bpcmusic/telex/extras/ii.png

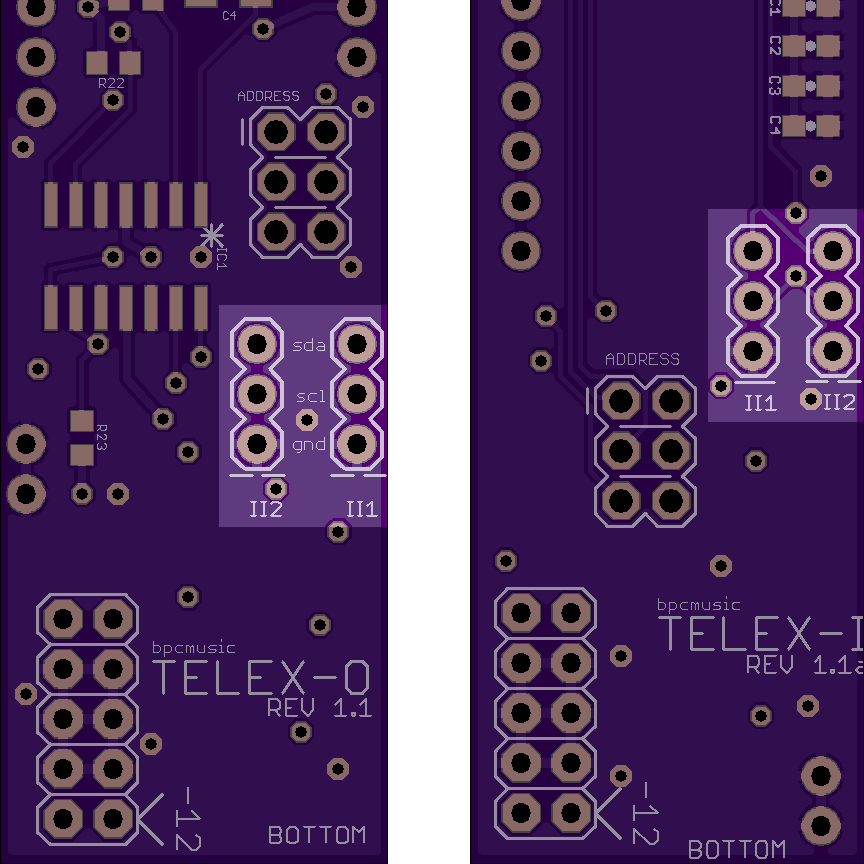
extras/ii.png
