bpcmusic/telex/extras/telex_address.png

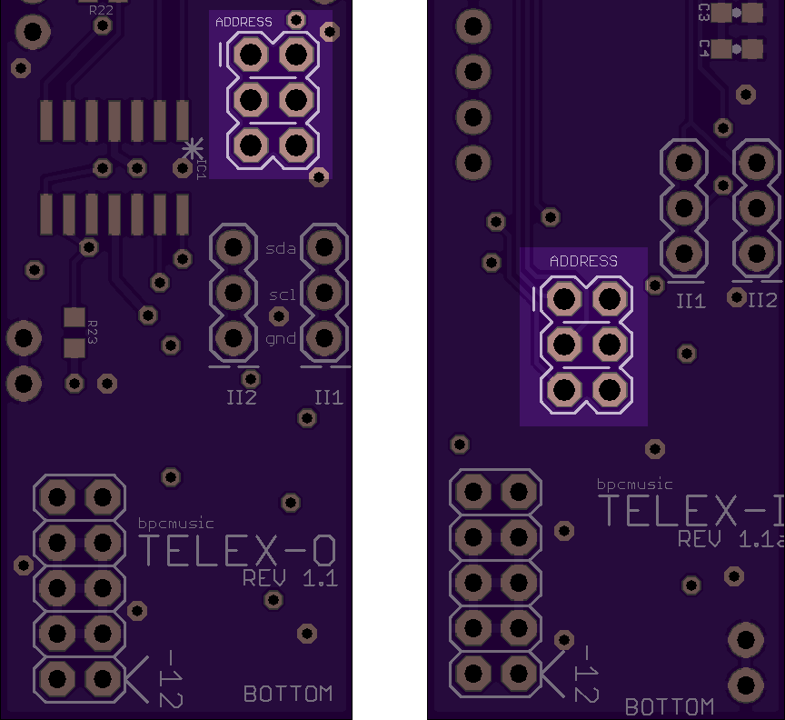
extras/telex_address.png
