bpcmusic/telex/hardware/TELEXi/board/images/TXi_Top_Top.png

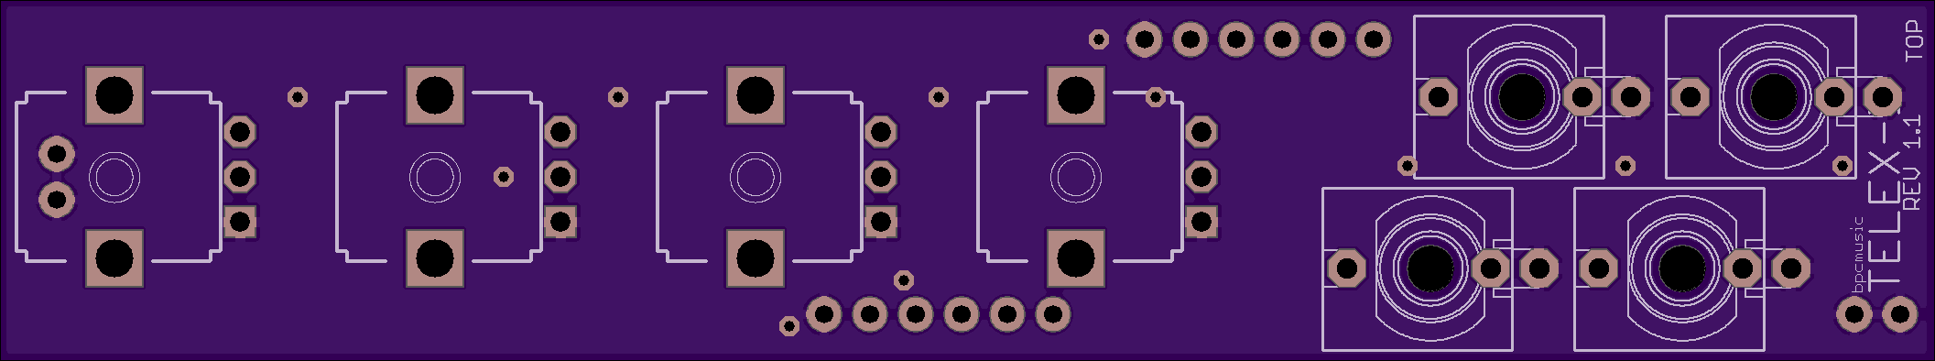
hardware/TELEXi/board/images/TXi_Top_Top.png
