bpcmusic/telex/hardware/TELEXi/board/stencil_frame/txi.png

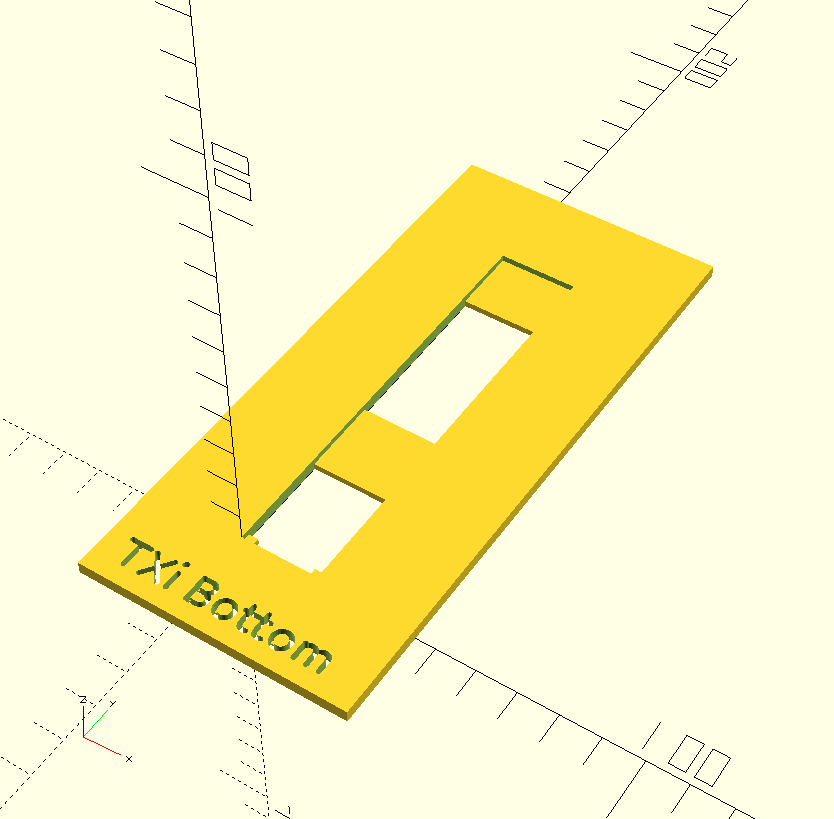
hardware/TELEXi/board/stencil_frame/txi.png
