bpcmusic/telex/hardware/TELEXo/board/images/TXo_Bottom_Top.png

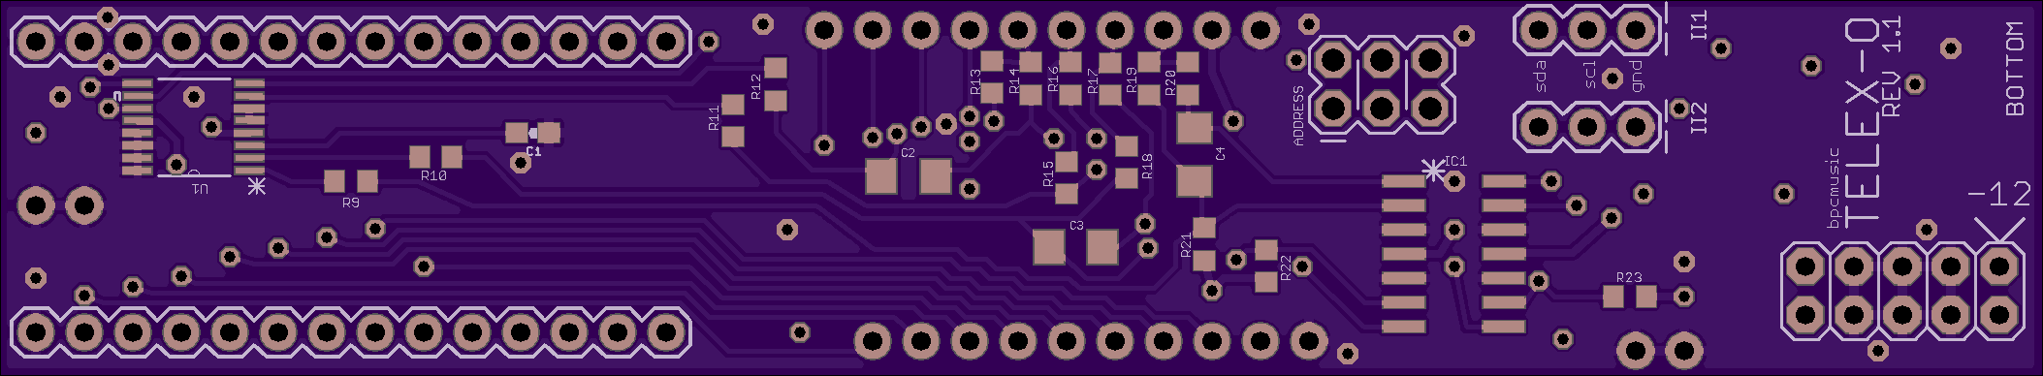
hardware/TELEXo/board/images/TXo_Bottom_Top.png
