bpcmusic/telex/hardware/TELEXo/board/stencil_frame/txo_bottom.png

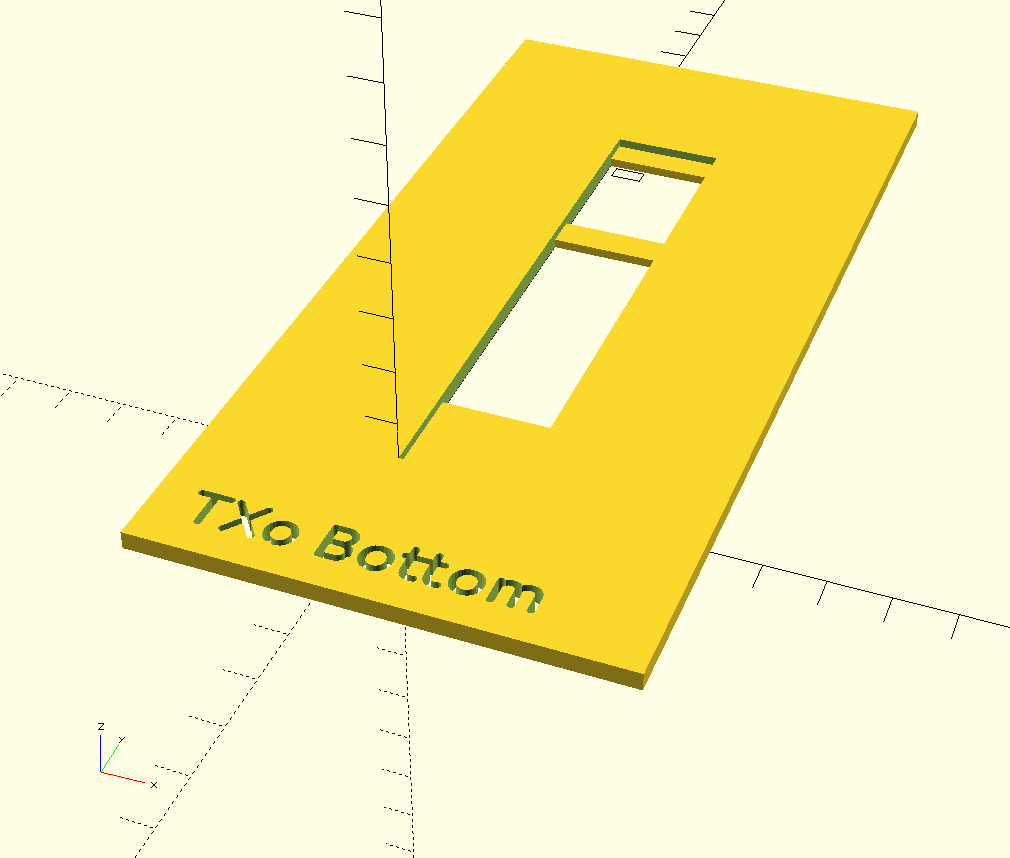
hardware/TELEXo/board/stencil_frame/txo_bottom.png
