bpcmusic/telex/hardware/TELEXo/board/stencil_frame/txo_top.png

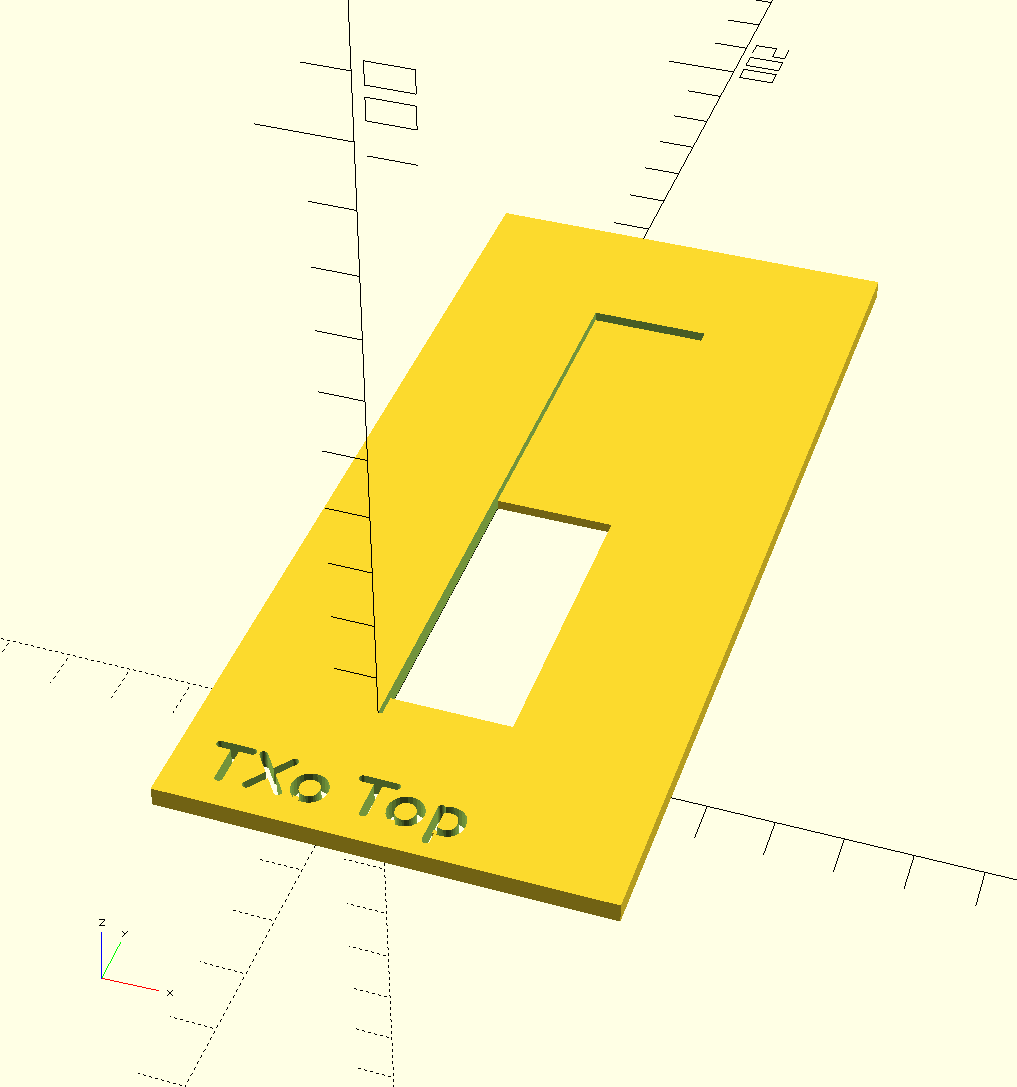
hardware/TELEXo/board/stencil_frame/txo_top.png
