bpcmusic/telex/telex.jpg

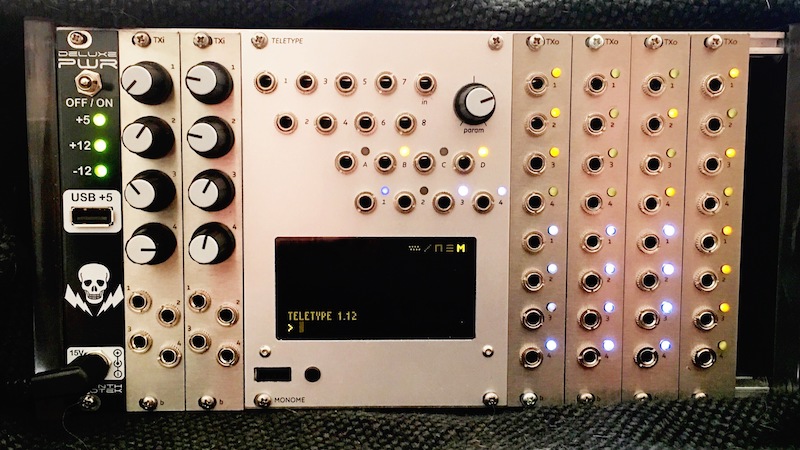
telex.jpg
