bpcmusic/telex/TX-MockUp.png

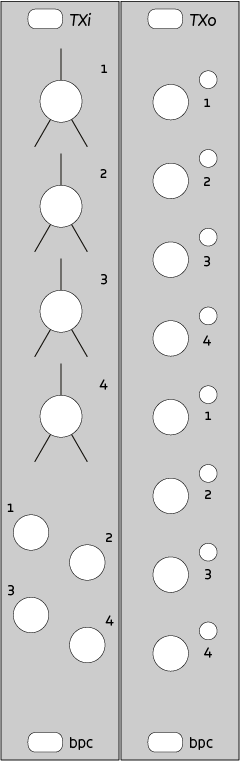
TX-MockUp.png
