bpcmusic/telex/hardware/TELEXi/board/build_map/tb/txi_tb_build_map.pdf

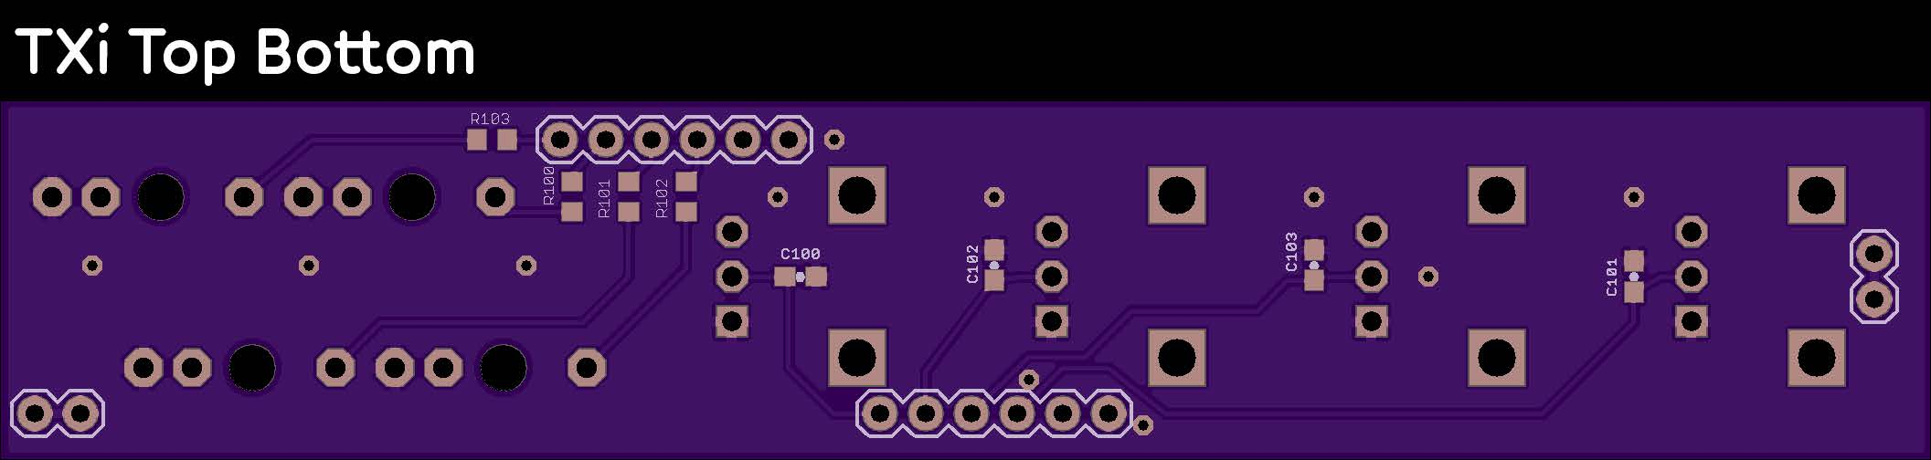
[picture p36: page 1]
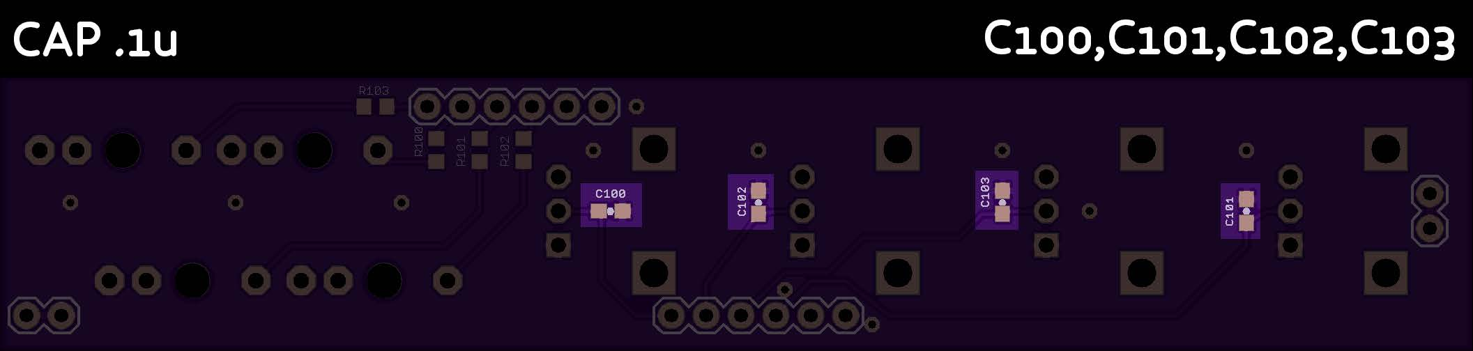
[picture p37: page 2]
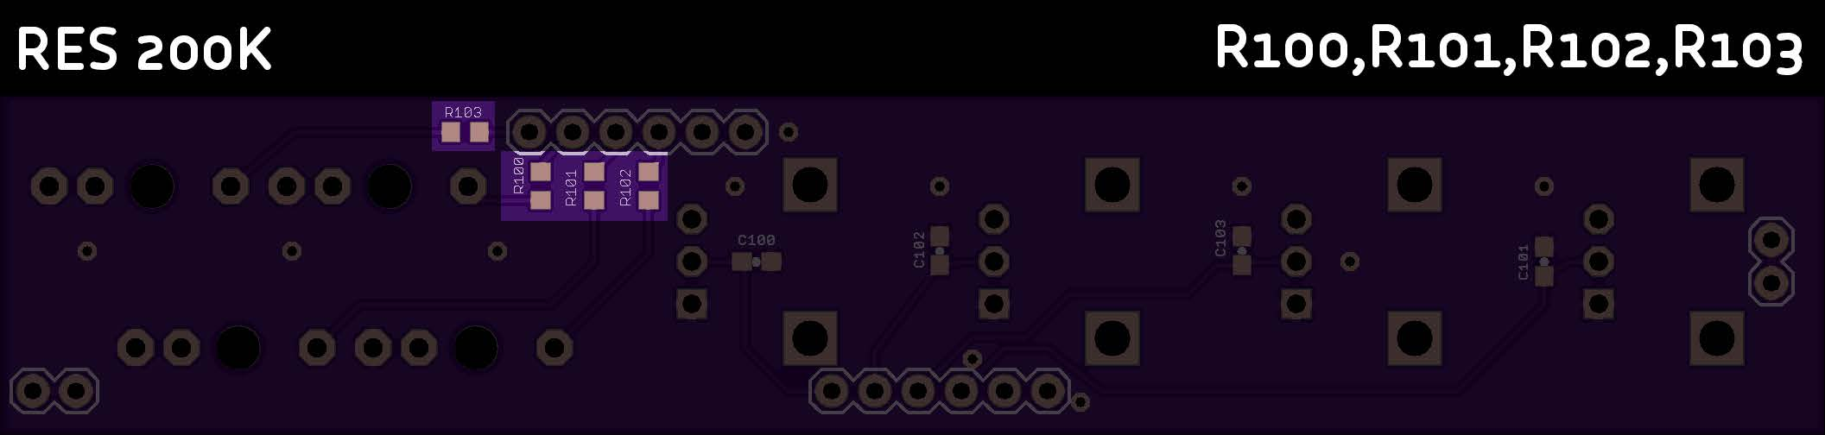
[picture p38: page 3]
