bpcmusic/telex/hardware/TELEXi/board/build_map/bb/00.png

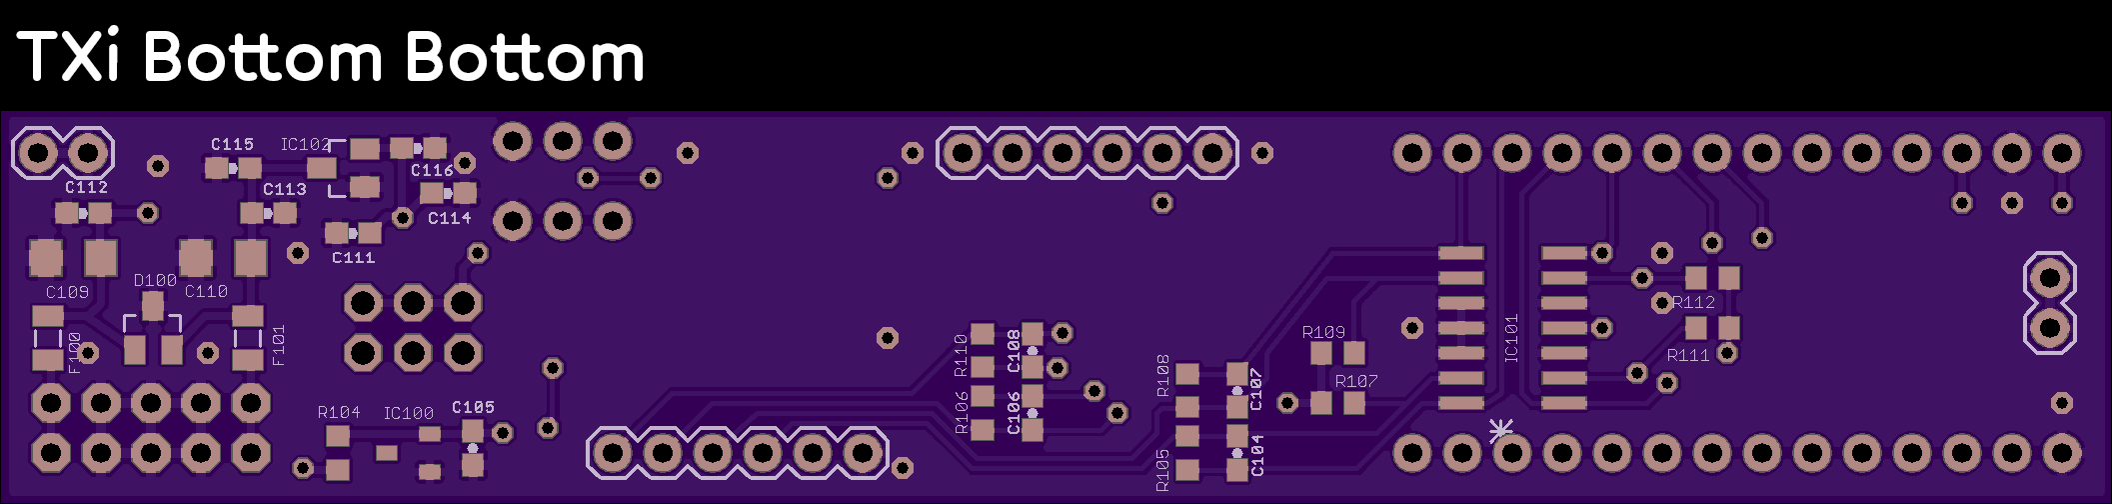
hardware/TELEXi/board/build_map/bb/00.png
