bpcmusic/telex/hardware/TELEXi/board/build_map/bb/01.png

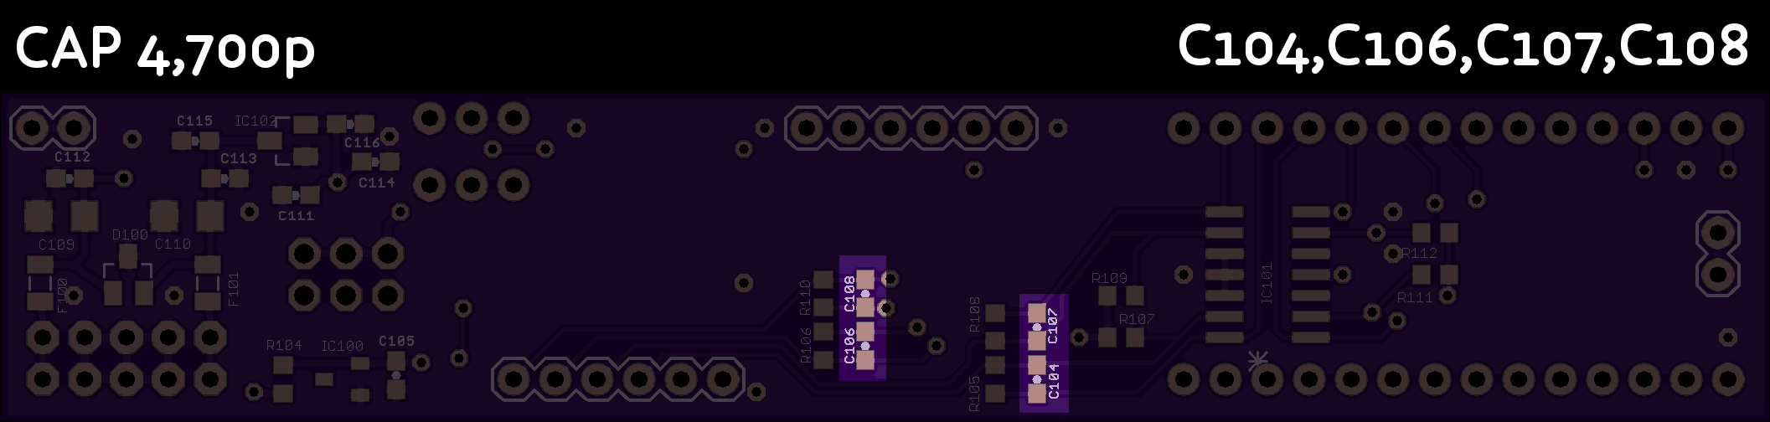
hardware/TELEXi/board/build_map/bb/01.png
