bpcmusic/telex/hardware/TELEXi/board/build_map/bb/02.png

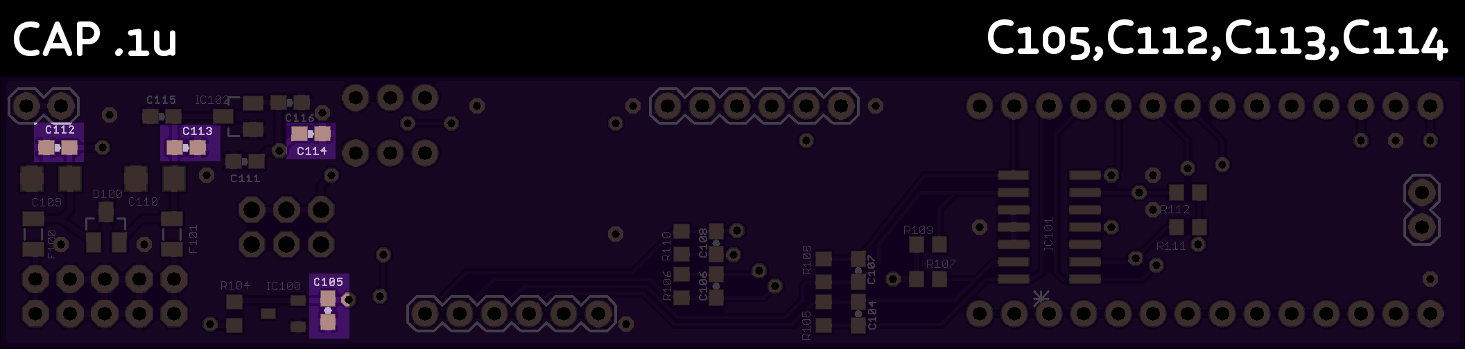
hardware/TELEXi/board/build_map/bb/02.png
