bpcmusic/telex/hardware/TELEXi/board/build_map/bb/03.png

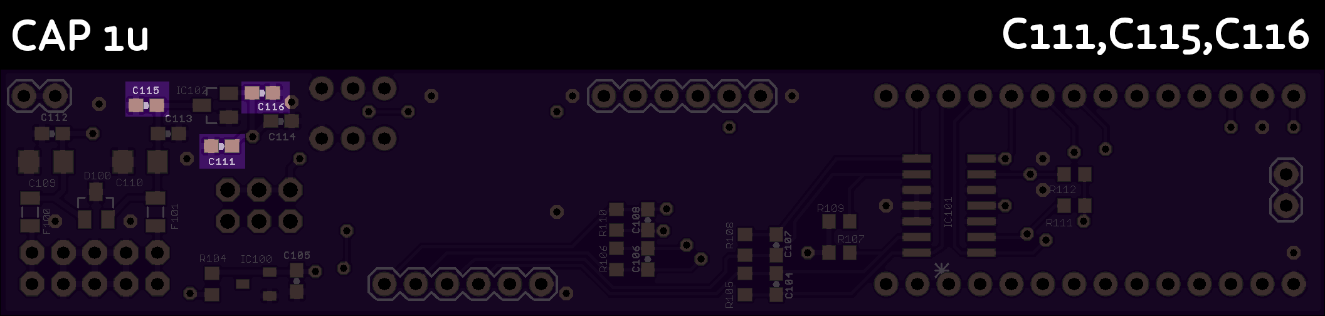
hardware/TELEXi/board/build_map/bb/03.png
