bpcmusic/telex/hardware/TELEXi/board/build_map/bb/04.png

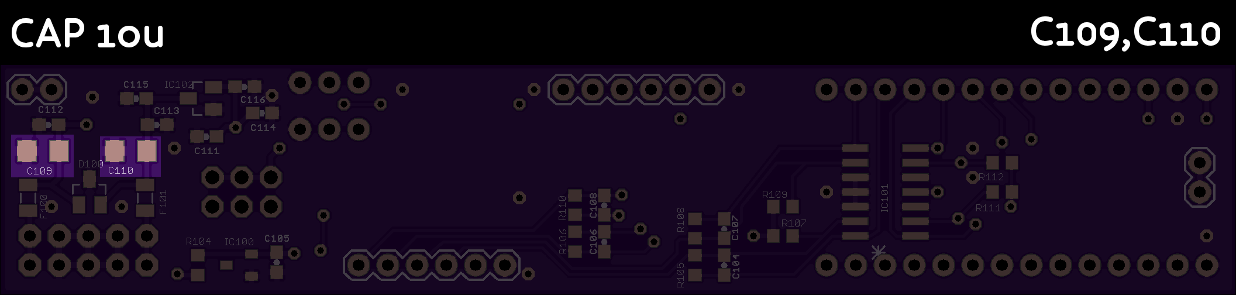
hardware/TELEXi/board/build_map/bb/04.png
