bpcmusic/telex/hardware/TELEXi/board/build_map/bb/06.png

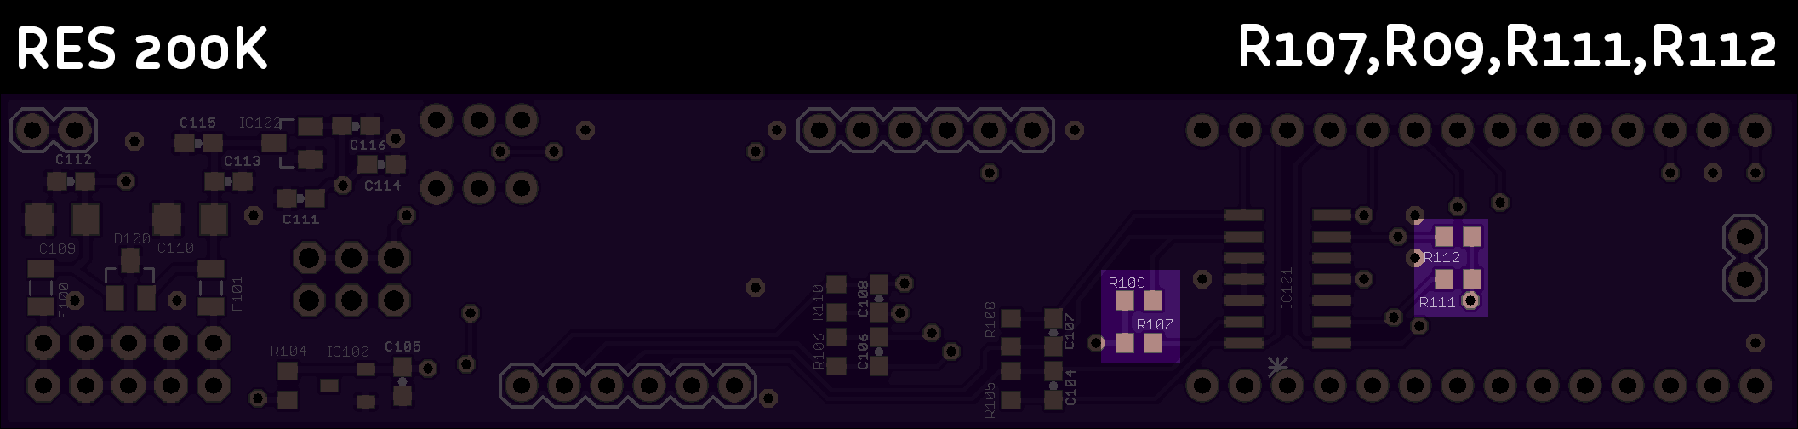
hardware/TELEXi/board/build_map/bb/06.png
