bpcmusic/telex/hardware/TELEXi/board/build_map/bb/08.png

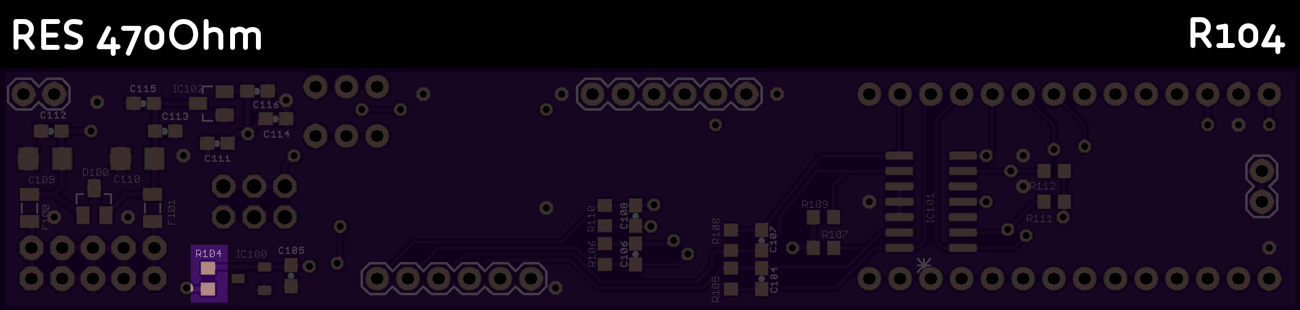
hardware/TELEXi/board/build_map/bb/08.png
