bpcmusic/telex/hardware/TELEXi/board/build_map/bb/09.png

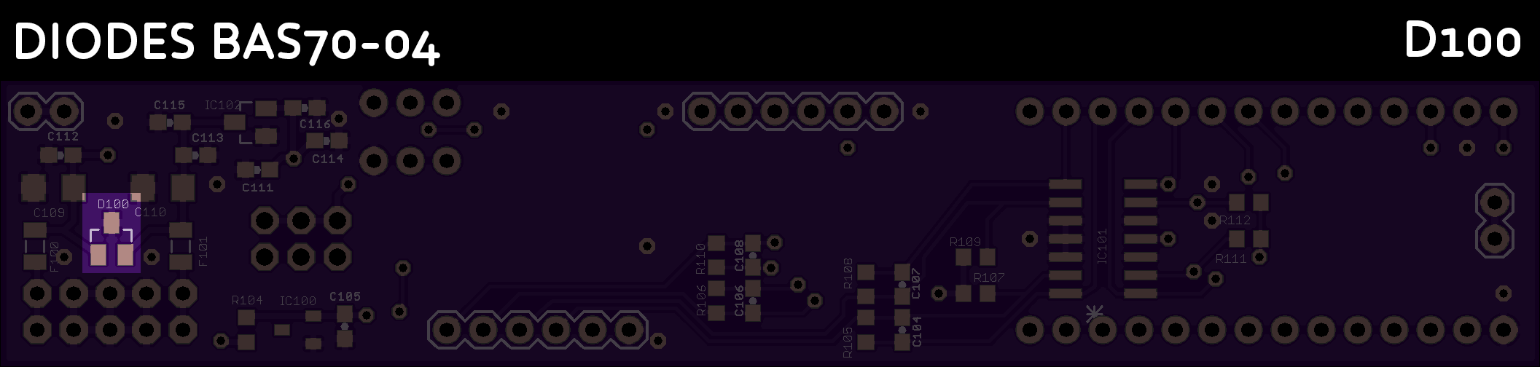
hardware/TELEXi/board/build_map/bb/09.png
