bpcmusic/telex/hardware/TELEXi/board/build_map/bb/10.png

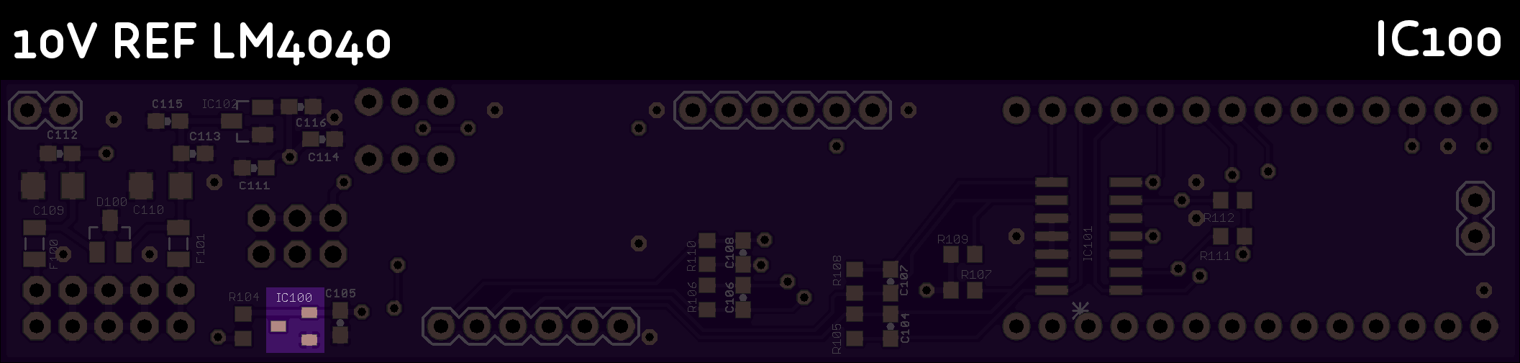
hardware/TELEXi/board/build_map/bb/10.png
