bpcmusic/telex/hardware/TELEXi/board/build_map/bb/11.png

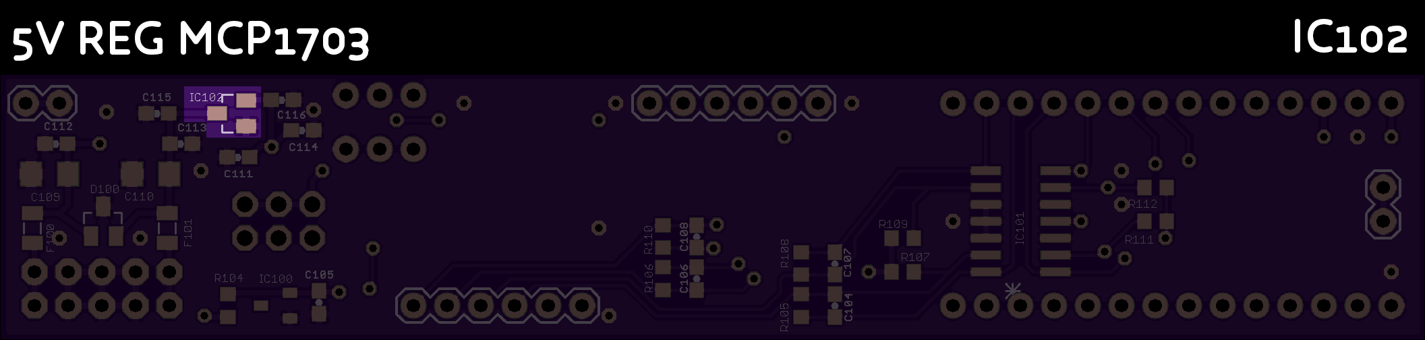
hardware/TELEXi/board/build_map/bb/11.png
