bpcmusic/telex/hardware/TELEXi/board/build_map/bb/12.png

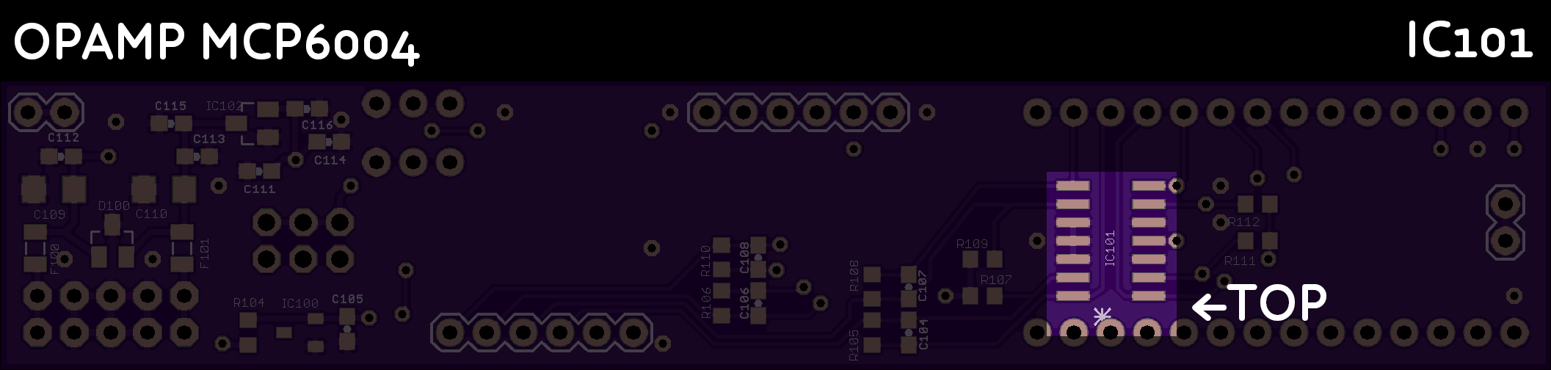
hardware/TELEXi/board/build_map/bb/12.png
