bpcmusic/telex/hardware/TELEXi/board/build_map/bt/00.png

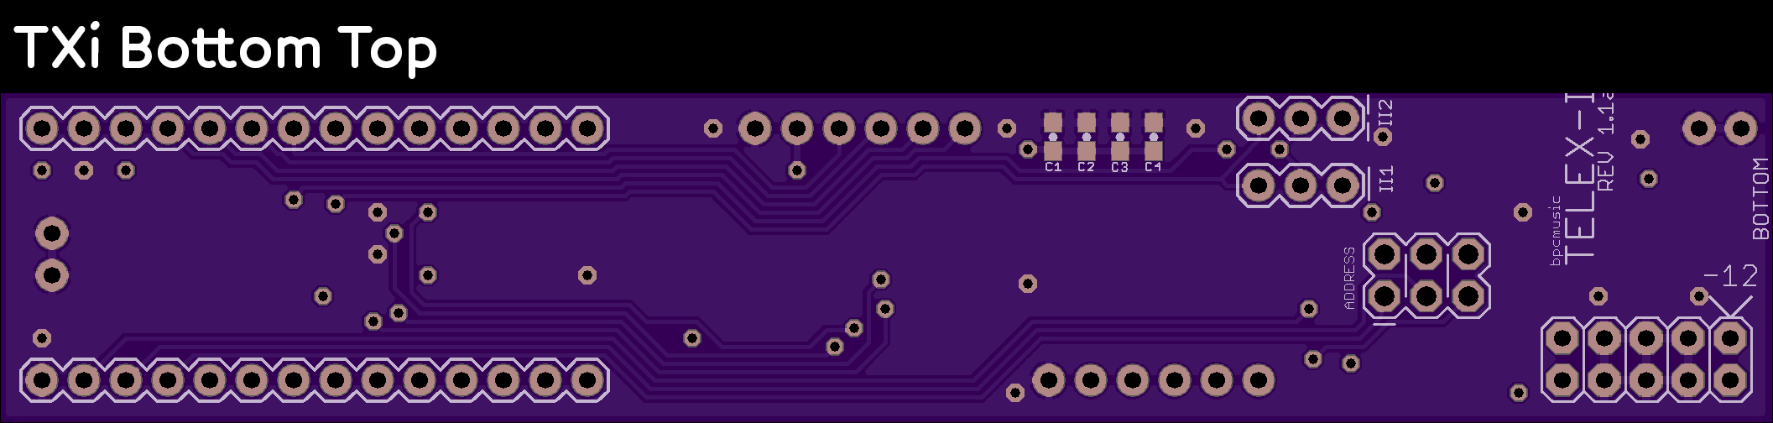
hardware/TELEXi/board/build_map/bt/00.png
