bpcmusic/telex/hardware/TELEXi/board/build_map/bt/01.png

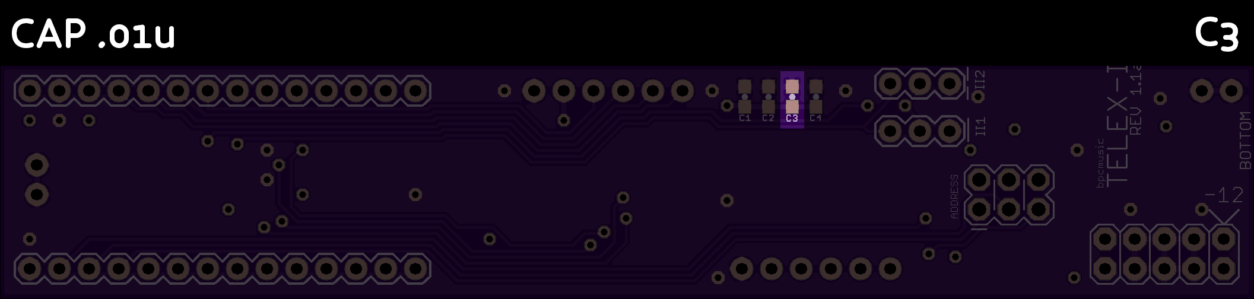
hardware/TELEXi/board/build_map/bt/01.png
