bpcmusic/telex/hardware/TELEXo/board/build_map/bb/00.png

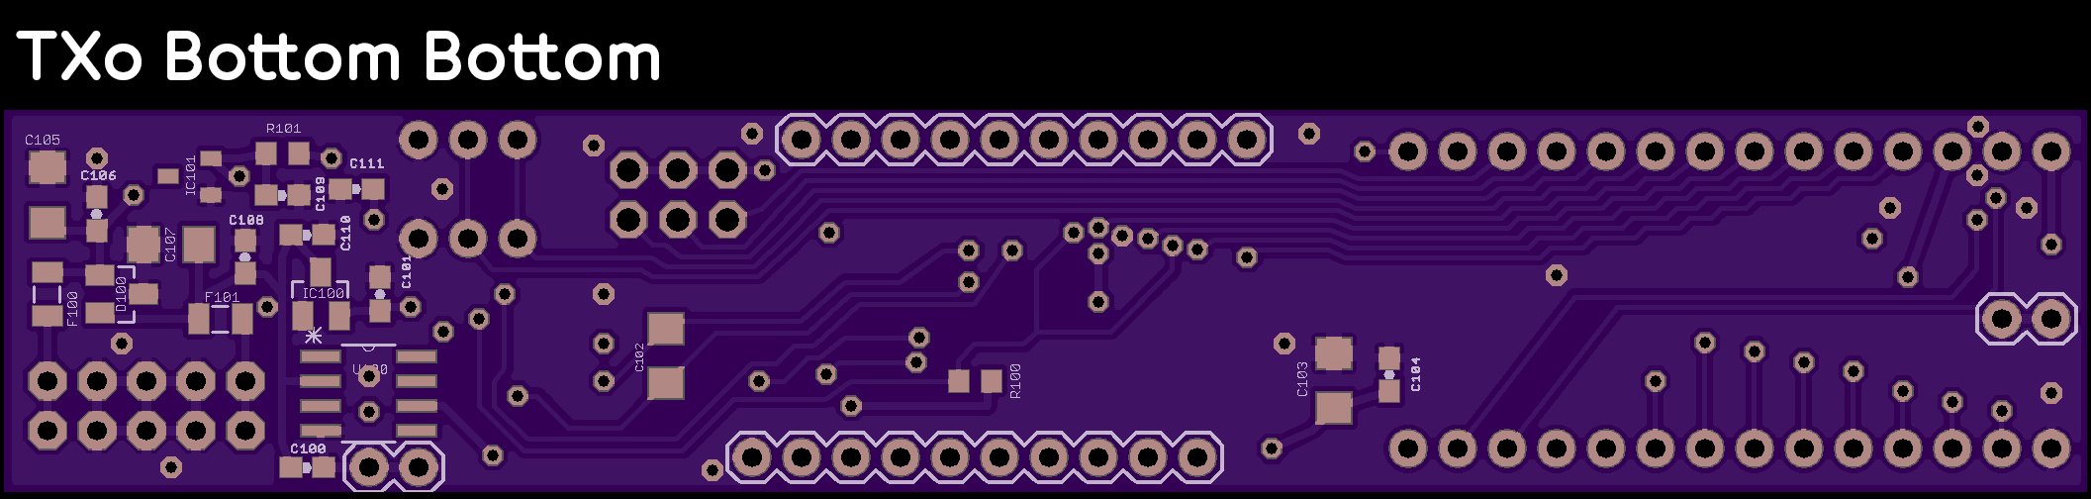
hardware/TELEXo/board/build_map/bb/00.png
