bpcmusic/telex/hardware/TELEXo/board/build_map/bb/01.png

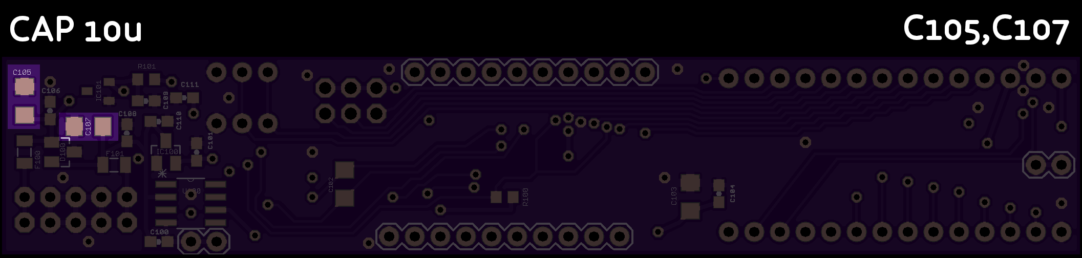
hardware/TELEXo/board/build_map/bb/01.png
