bpcmusic/telex/hardware/TELEXo/board/build_map/bb/02.png

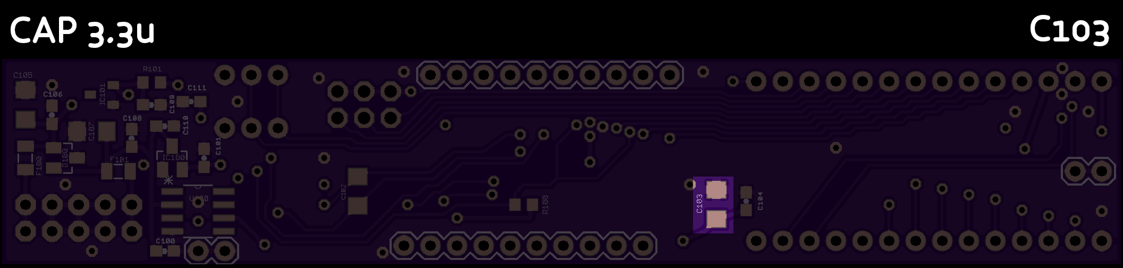
hardware/TELEXo/board/build_map/bb/02.png
