bpcmusic/telex/hardware/TELEXo/board/build_map/bb/03.png

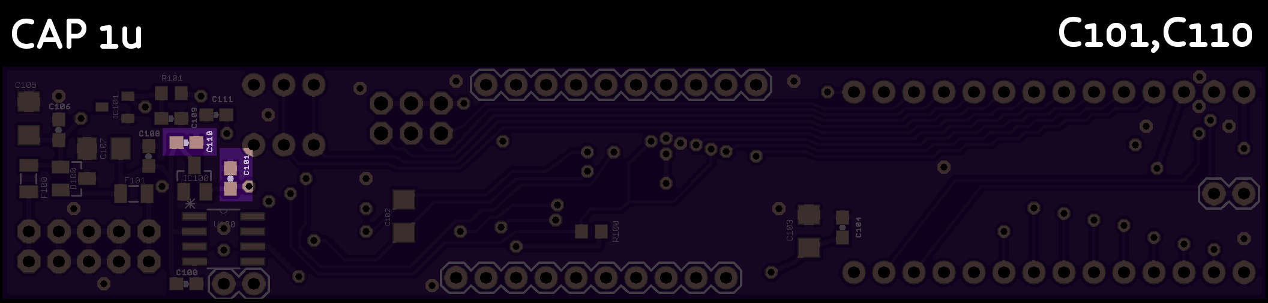
hardware/TELEXo/board/build_map/bb/03.png
