bpcmusic/telex/hardware/TELEXo/board/build_map/bb/04.png

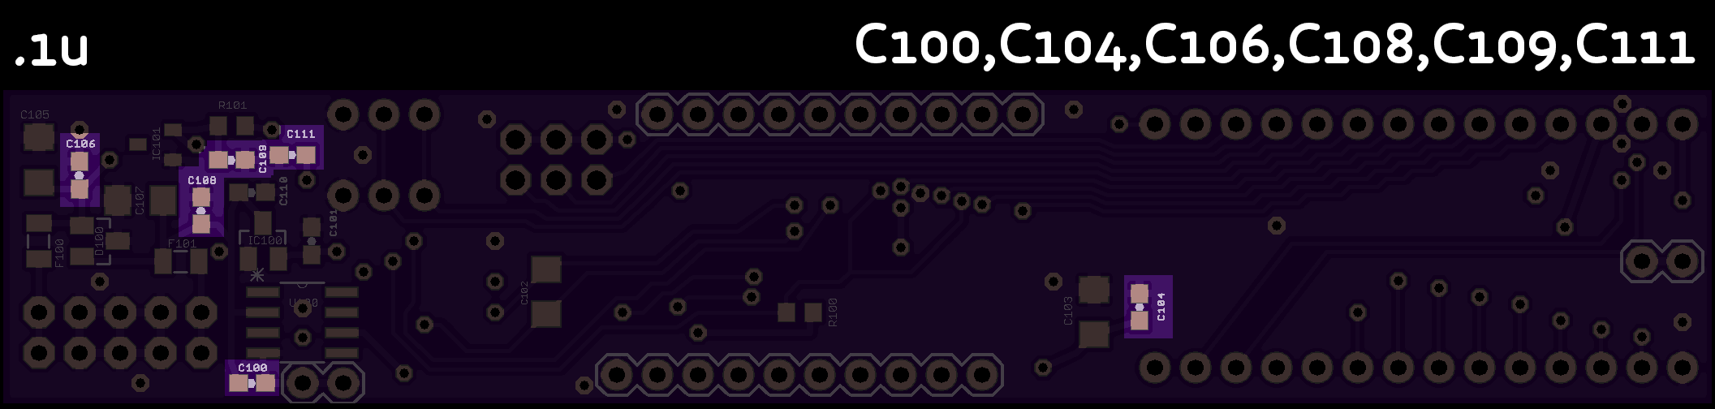
hardware/TELEXo/board/build_map/bb/04.png
