bpcmusic/telex/hardware/TELEXo/board/build_map/bb/05.png

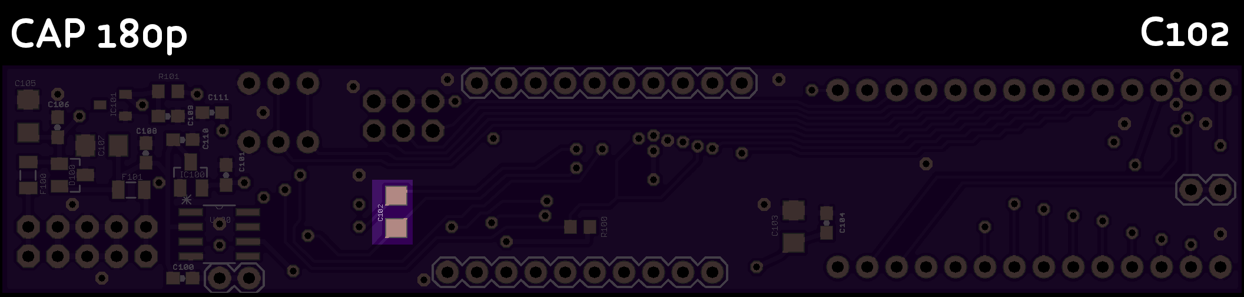
hardware/TELEXo/board/build_map/bb/05.png
