bpcmusic/telex/hardware/TELEXo/board/build_map/bb/09.png

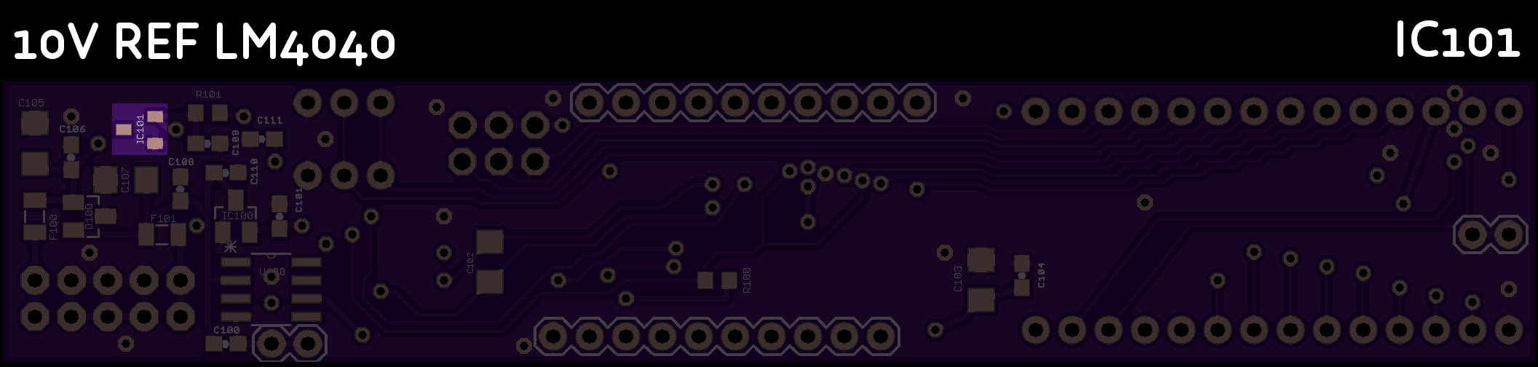
hardware/TELEXo/board/build_map/bb/09.png
