bpcmusic/telex/hardware/TELEXo/board/build_map/bb/10.png

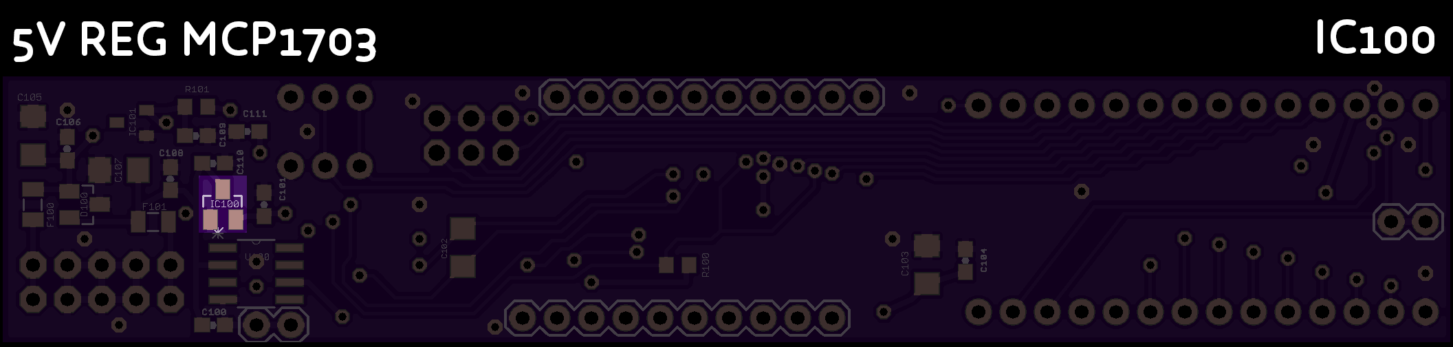
hardware/TELEXo/board/build_map/bb/10.png
