bpcmusic/telex/hardware/TELEXo/board/build_map/bb/11.png

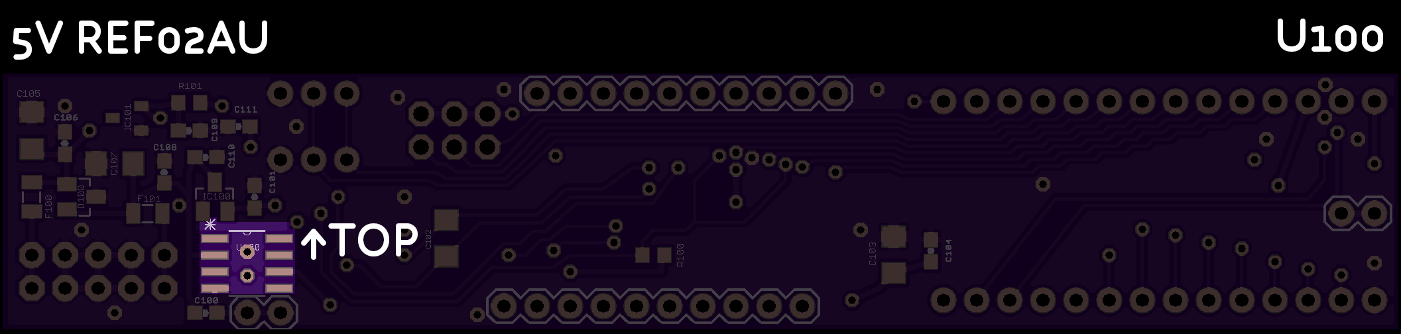
hardware/TELEXo/board/build_map/bb/11.png
