bpcmusic/telex/hardware/TELEXo/board/build_map/bb/12.png

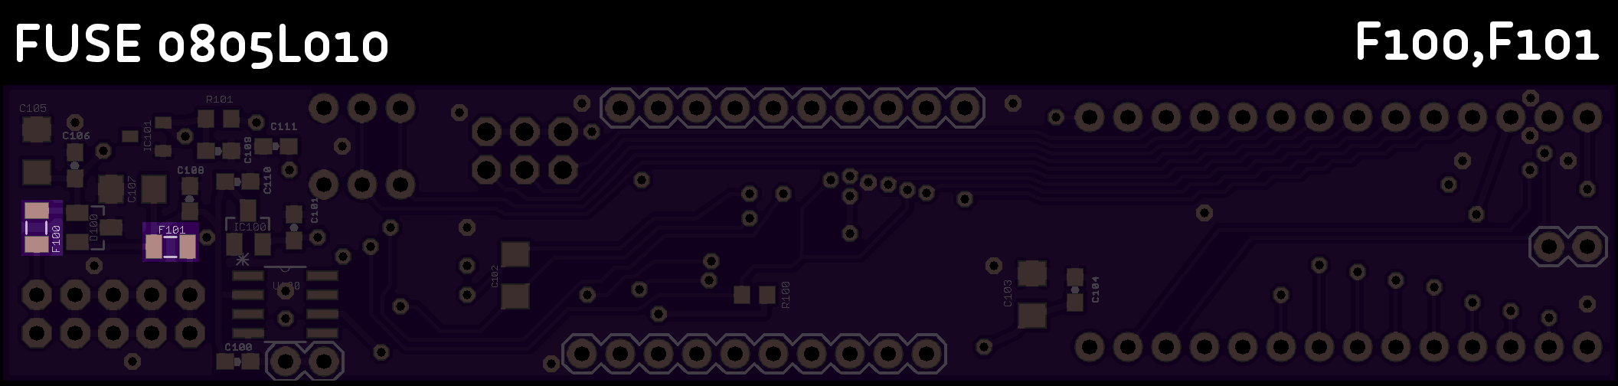
hardware/TELEXo/board/build_map/bb/12.png
