bpcmusic/telex/hardware/TELEXo/board/build_map/bt/00.png

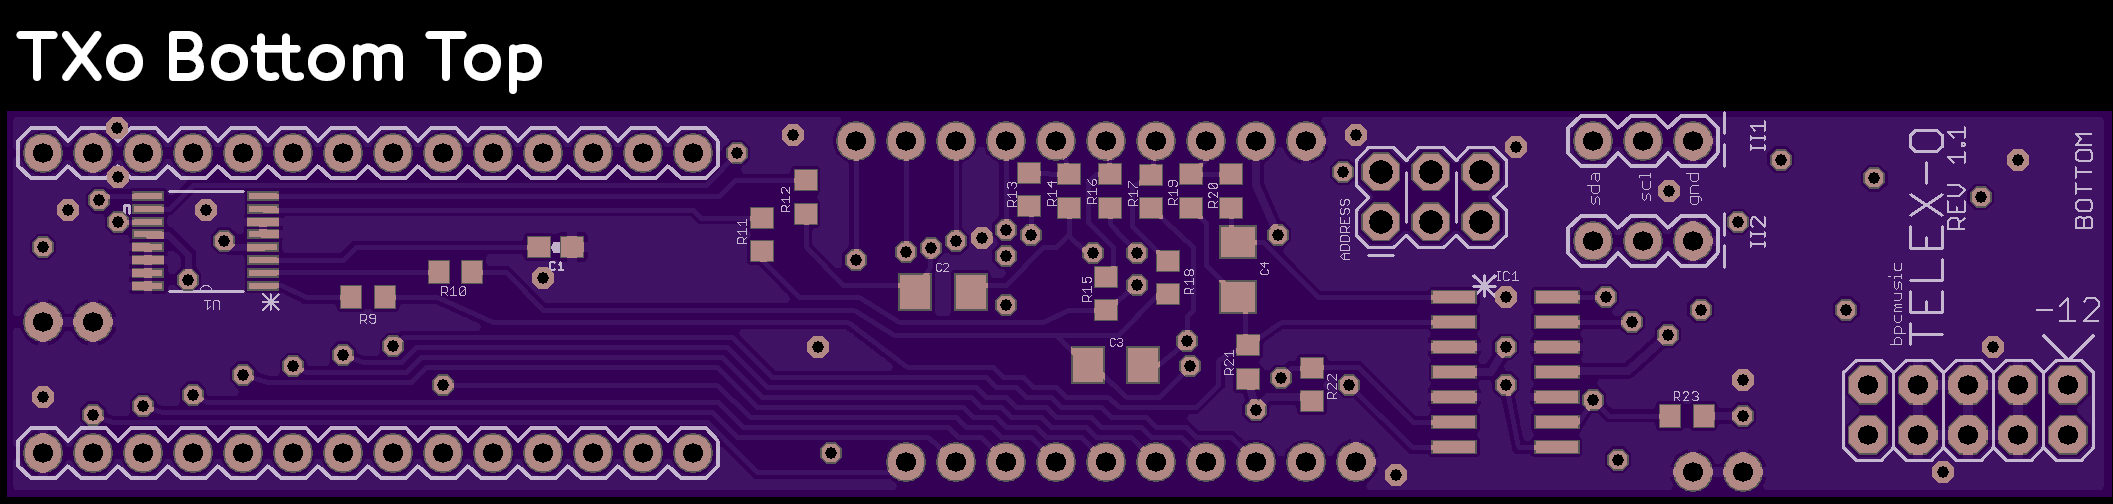
hardware/TELEXo/board/build_map/bt/00.png
