bpcmusic/telex/hardware/TELEXo/board/build_map/bt/01.png

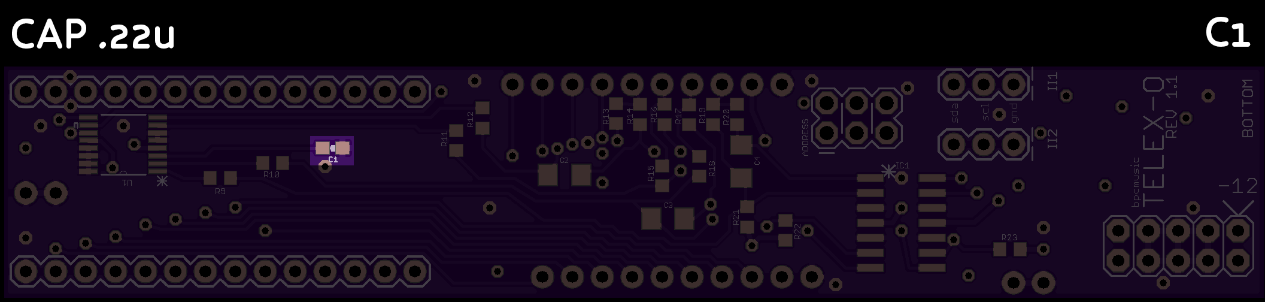
hardware/TELEXo/board/build_map/bt/01.png
