bpcmusic/telex/hardware/TELEXo/board/build_map/bt/02.png

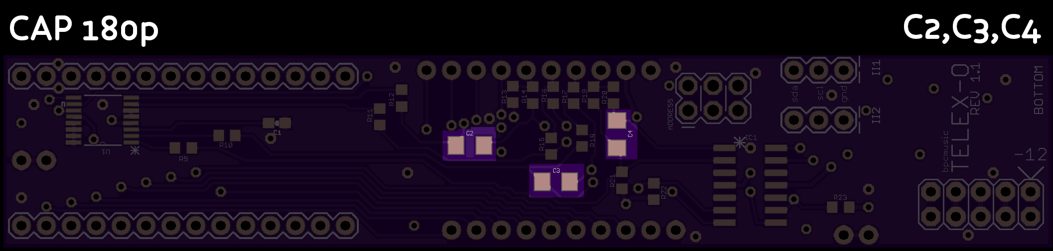
hardware/TELEXo/board/build_map/bt/02.png
