bpcmusic/telex/hardware/TELEXo/board/build_map/bt/03.png

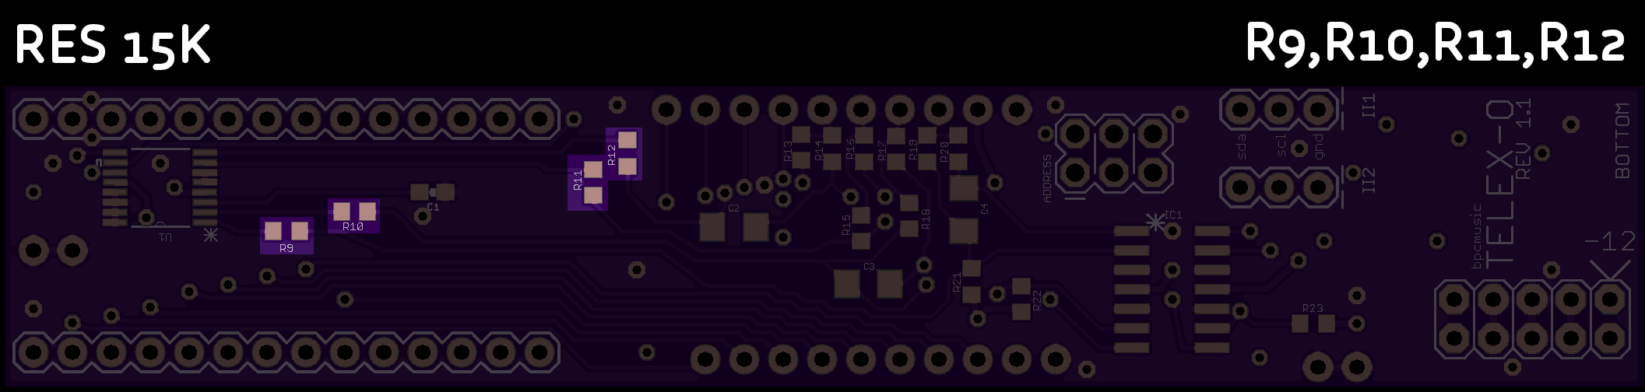
hardware/TELEXo/board/build_map/bt/03.png
