bpcmusic/telex/hardware/TELEXo/board/build_map/bt/04.png

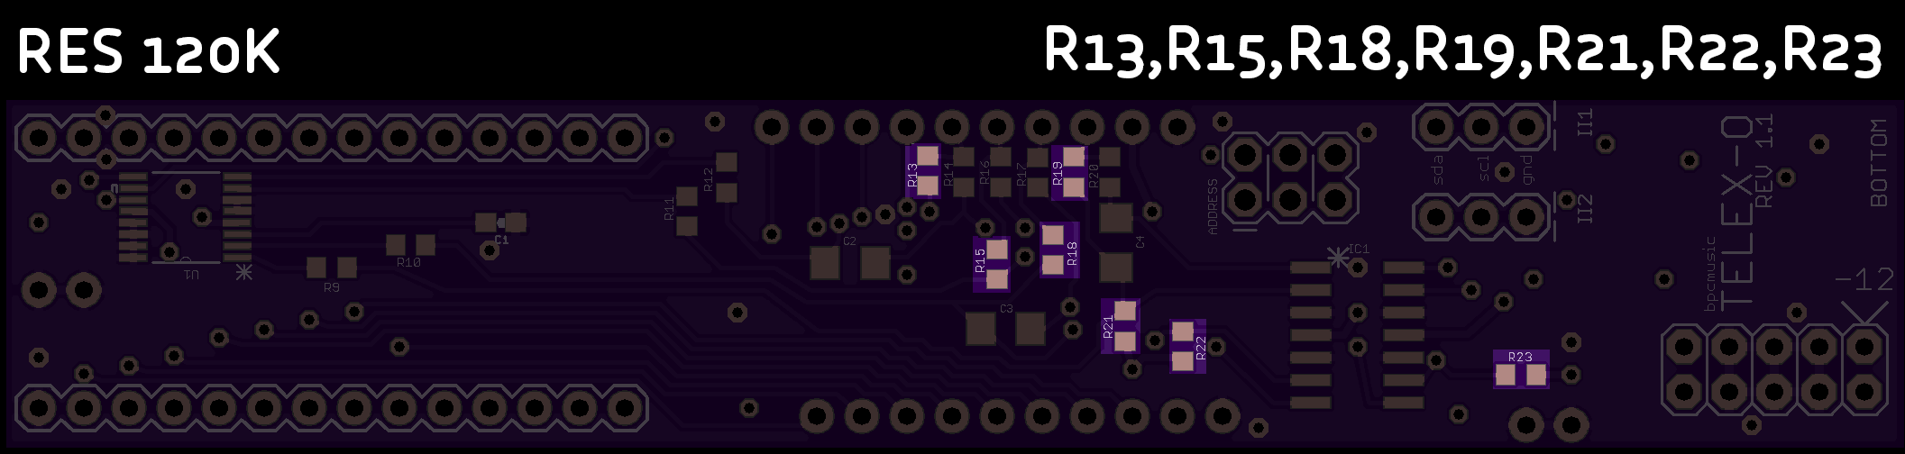
hardware/TELEXo/board/build_map/bt/04.png
