bpcmusic/telex/hardware/TELEXo/board/build_map/bt/05.png

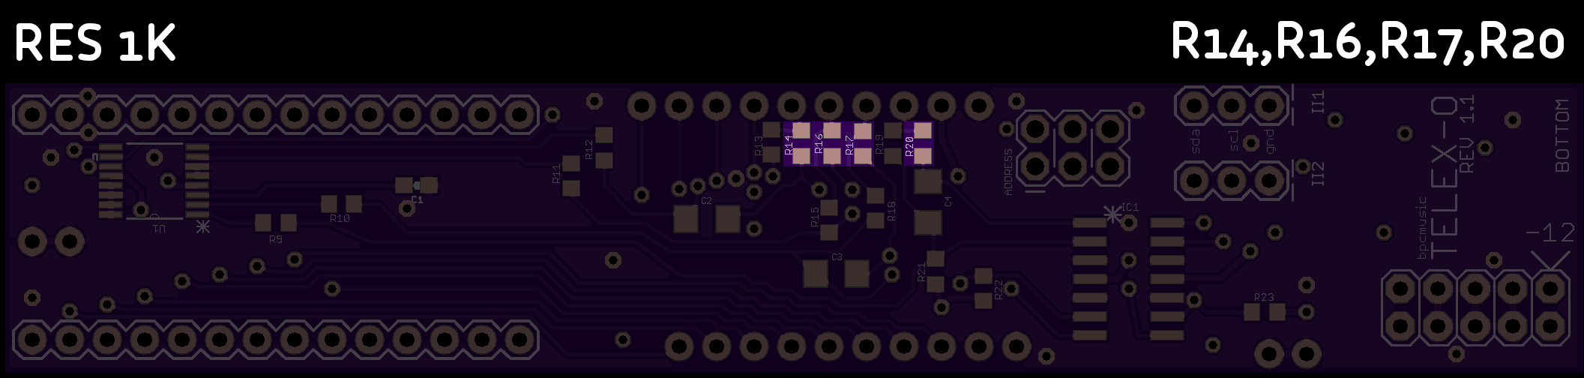
hardware/TELEXo/board/build_map/bt/05.png
