bpcmusic/telex/hardware/TELEXo/board/build_map/bt/06.png

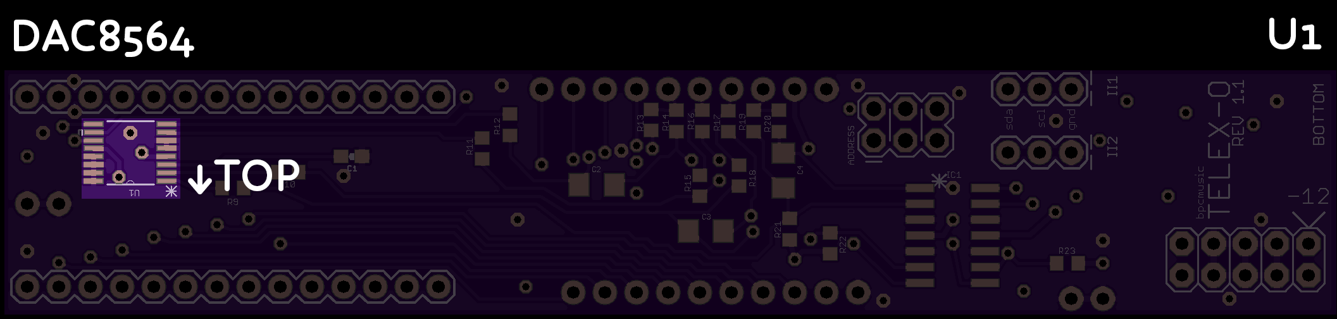
hardware/TELEXo/board/build_map/bt/06.png
