bpcmusic/telex/hardware/TELEXo/board/build_map/bt/07.png

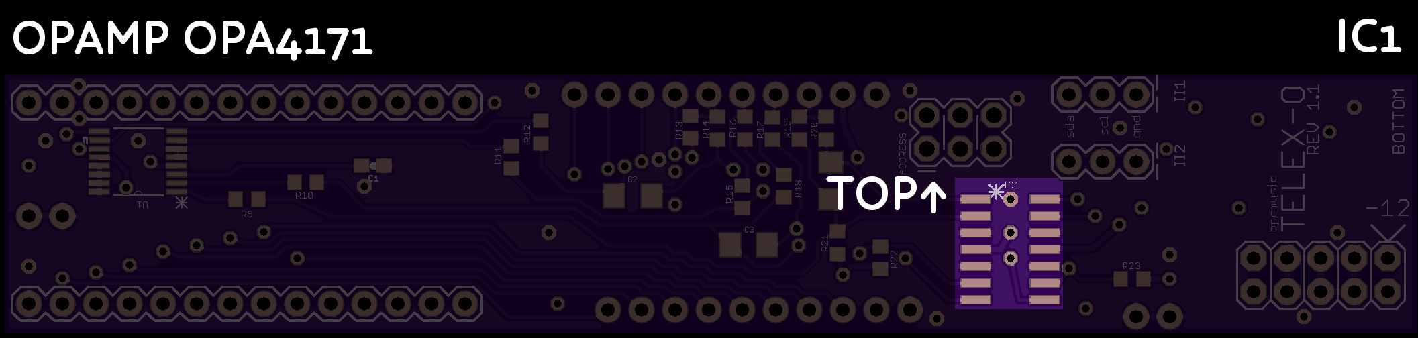
hardware/TELEXo/board/build_map/bt/07.png
