bpcmusic/telex/hardware/TELEXo/board/build_map/tb/00.png

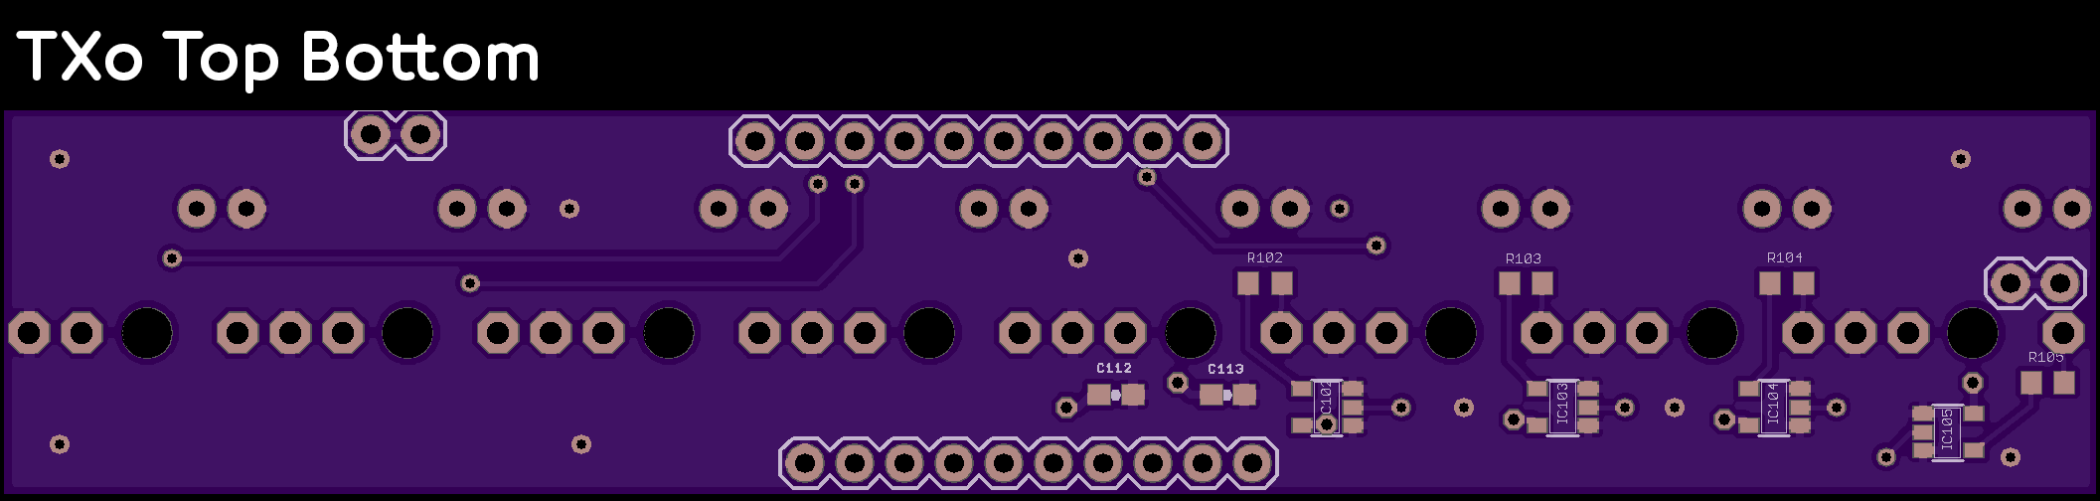
hardware/TELEXo/board/build_map/tb/00.png
