bpcmusic/telex/hardware/TELEXo/board/build_map/tb/01.png

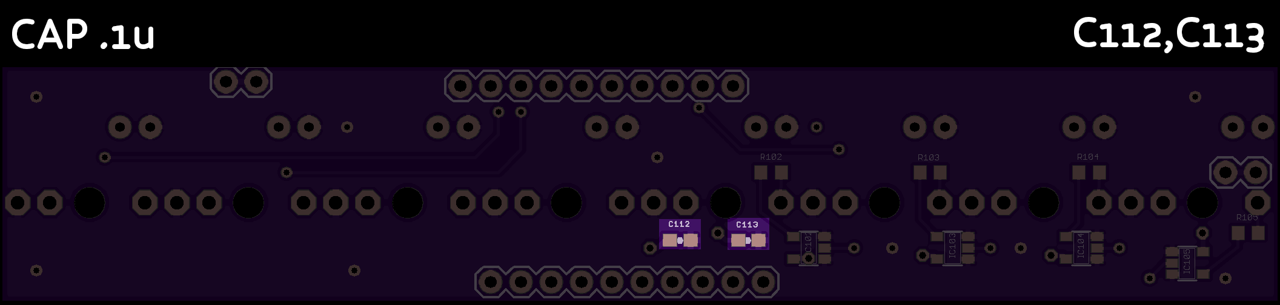
hardware/TELEXo/board/build_map/tb/01.png
