bpcmusic/telex/hardware/TELEXo/board/build_map/tb/02.png

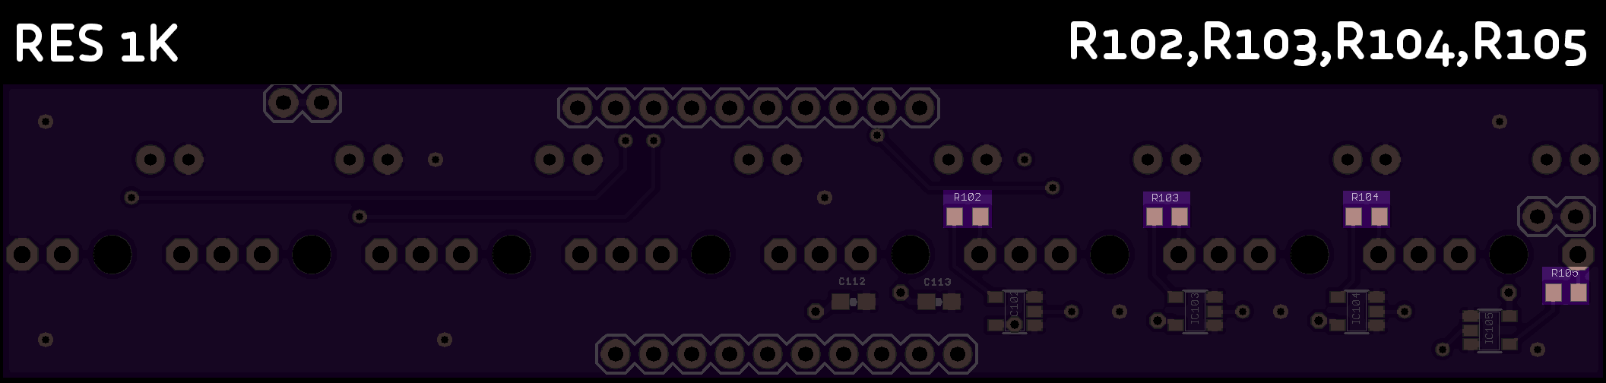
hardware/TELEXo/board/build_map/tb/02.png
