bpcmusic/telex/hardware/TELEXo/board/build_map/tb/03.png

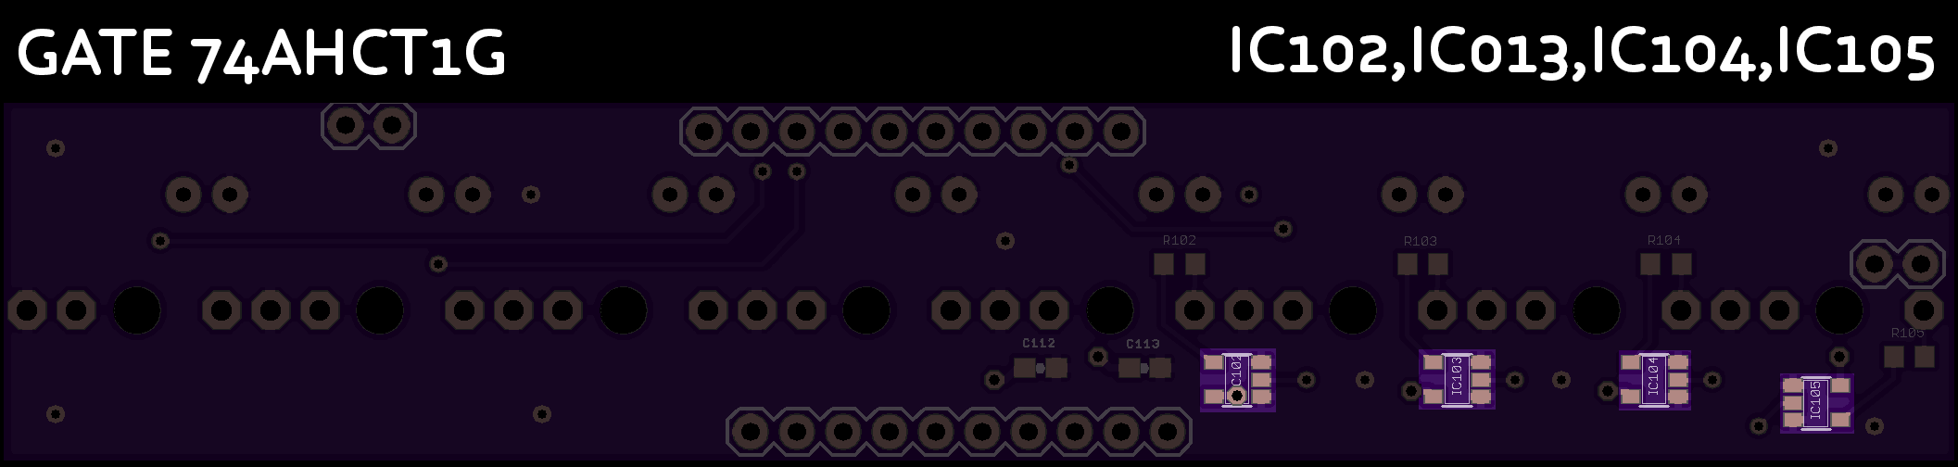
hardware/TELEXo/board/build_map/tb/03.png
