bpcmusic/telex/hardware/TELEXo/board/build_map/tt/00.png

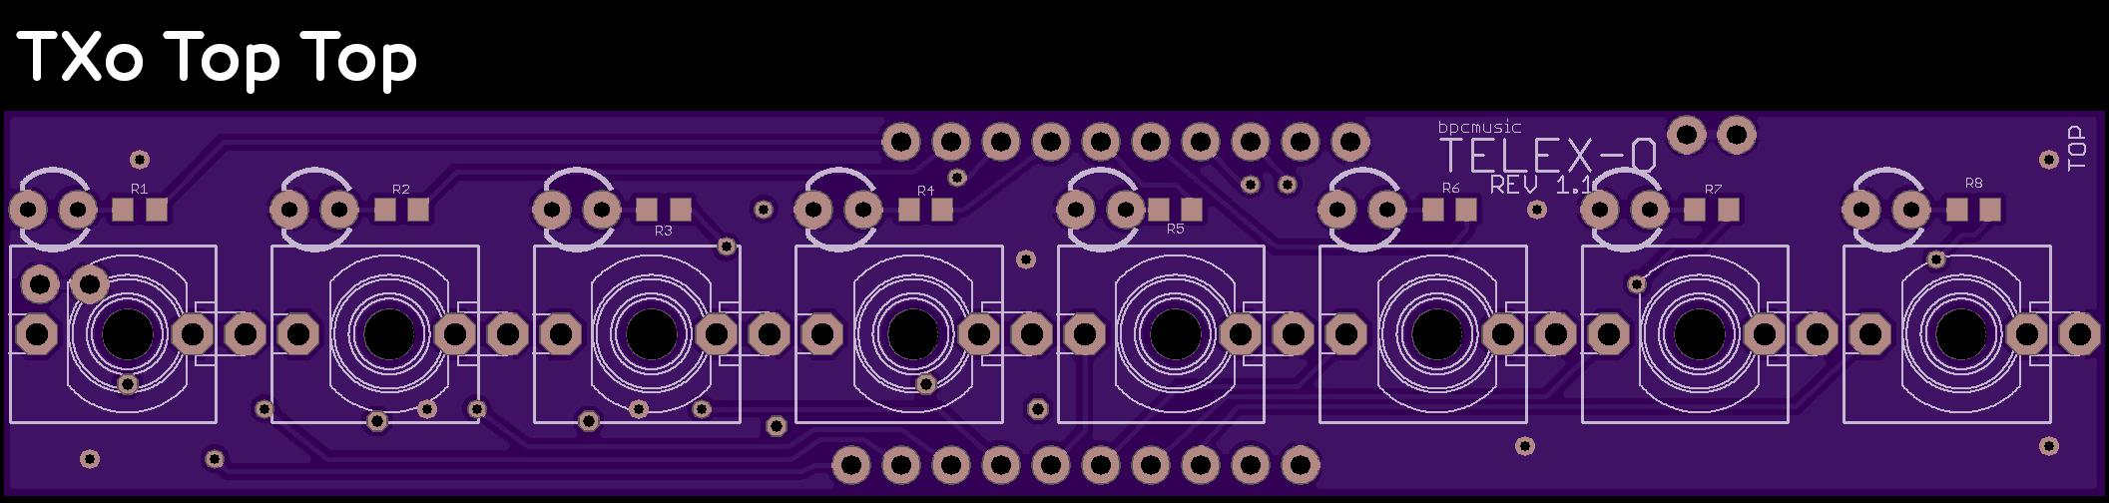
hardware/TELEXo/board/build_map/tt/00.png
