bpcmusic/telex/software/TELEXo/Quantizer.cpp

/*
 * TELEXo Eurorack Module
 * (c) 2016, 2017 Brendon Cassidy
 * MIT License
 */
 
#include "Arduino.h"
#include "Quantizer.h"
#include "TxHelper.h"

/*
 * initializes the quantizer and sets the scale to 0 (usually equal temperment)
 */
Quantizer::Quantizer() {
  Quantizer(0);
}

/*
 * initializes the quantizer and sets the initial scale
 */
Quantizer::Quantizer(int scale) {
  SetScale(scale);
  
  _last.Note = 0;
  _last.Value = 0;
  
  _below = 0;
  _above = 0;
  _noteMode = false;
}

/*
 * change the scale of the quantizer
 */
void Quantizer::SetScale(int scale) {
  if (scale < scaleCount)
    _scale = scale;
}

/*
 * quantizes an int (range 0-16383)
 */
QuantizeResponse Quantizer::Quantize(int in) {

  QuantizeResponse response;

  // deal with negative values
  in = in < 0 ? abs(in) : in;

  // short circuit if we are within our current bounary
  if (in >= _below && in < _above){
    return _last;
  }
  
  // if not - we need to find where we are in the list
  // hints are a type of skip-list that jumps us to the proper octave
  _octave = (int)(in / 1638.3) - 1;
  _octave = _octave > 0 ? _octave : 0;
  
  _index = hints[_scale][_octave];

  int distance = 32768;
  int distanceTemp = 0;

  // find where we can't get any closer then back out
  while (_index < notecount[_scale]) {

    _temp = in - scales[_scale][_index];
    
    distanceTemp = abs(_temp);

    if (distanceTemp > distance){
      _index--;
      break;
    } else {
      // else increment
      distance = distanceTemp;
      _index++;
    }
    
  }

  // move it down to the next to last if we made it to the end
  if (_index >= notecount[_scale]) 
    _index = notecount[_scale] - 1;
  
  // use index to quantize
  _current = scales[_scale][_index];

  // set the response
  response.Note = _index;
  response.Value = _current;
  response.Frequency = freqs[_scale][_index];
  
  _last = response;
  
  // now set the helper boundries
  _above = _index < notecount[_scale] - 1 ? scales[_scale][_index + 1] : 32767;
  _below = _index > 0 ? scales[_scale][_index-1] : scales[_scale][_index];

  // similar to a mutable quantize trick to expand the region slightly
  // had been doing this using floats - thx for the fixed math tip Émilie
  _above = ((13 * _current) + (19 * _above)) >> 5;
  _below = ((13 * _current) + (19 * _below)) >> 5;

  // constrain the above and below values
  _above = _above > 32767 ? 32767 : _above;
  _below = _below < 0 ? 0 : _below;

  return response;
  
}

/*
 * returns the values (0-16383) for a note number; 0 if out of range
 */
float Quantizer::GetValueForNote(int note){
  if (note < notecount[_scale])
    return scales[_scale][note];
  else
    return 0;
}

float Quantizer::GetFrequencyForNote(int note){
  if (note < notecount[_scale])
    return freqs[_scale][note];
  else
    return 0;
}


// INSERT AUTOGENERATED SCALE CLASS DATA HERE

// scl/~equal_temperament.scl
// Standard 12 Tone Equal Temperament
const float Quantizer::scale0[] = { 0.0,136.525,273.05,409.575,546.1,682.625,819.15,955.675,1092.2,1228.725,1365.25,1501.775,1638.3,1774.825,1911.35,2047.875,2184.4,2320.925,2457.45,2593.975,2730.5,2867.025,3003.55,3140.075,3276.6,3413.125,3549.65,3686.175,3822.7,3959.225,4095.75,4232.275,4368.8,4505.325,4641.85,4778.375,4914.9,5051.425,5187.95,5324.475,5461.0,5597.525,5734.05,5870.575,6007.1,6143.625,6280.15,6416.675,6553.2,6689.725,6826.25,6962.775,7099.3,7235.825,7372.35,7508.875,7645.4,7781.925,7918.45,8054.975,8191.5,8328.025,8464.55,8601.075,8737.6,8874.125,9010.65,9147.175,9283.7,9420.225,9556.75,9693.275,9829.8,9966.325,10102.85,10239.375,10375.9,10512.425,10648.95,10785.475,10922.0,11058.525,11195.05,11331.575,11468.1,11604.625,11741.15,11877.675,12014.2,12150.725,12287.25,12423.775,12560.3,12696.825,12833.35,12969.875,13106.4,13242.925,13379.45,13515.975,13652.5,13789.025,13925.55,14062.075,14198.6,14335.125,14471.65,14608.175,14744.7,14881.225,15017.75,15154.275,15290.8,15427.325,15563.85,15700.375,15836.9,15973.425,16109.95,16246.475,16383.0,16519.525 };
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
8962,8476.66831574 };
const int Quantizer::hints14[] = { 0,44,87,129,173,216,259,302,345,388,431 };
// scl/partch-indian.scl
// Partch's Indian Chromatic, Exposition of Monophony, 1933.
const float Quantizer::scale15[] = { 0.0,72.730885745,143.29037282,205.657244118,278.388129863,364.345503876,430.929267078,527.414797854,593.998561056,679.955935069,752.686820813,795.274770953,905.227958028,958.344064931,1044.30143894,1068.29725201,1164.00130905,1236.73219479,1322.68956881,1413.02797704,1485.75886279,1565.56911426,1638.3,1711.03088574,1781.59037282,1843.95724412,1916.68812986,2002.64550388,2069.22926708,2165.71479785,2232.29856106,2318.25593507,2390.98682081,2433.57477095,2543.52795803,2596.64406493,2682.60143894,2706.59725201,2802.30130905,2875.03219479,2960.98956881,3051.32797704,3124.05886279,3203.86911426,3276.6,3349.33088574,3419.89037282,3482.25724412,3554.98812986,3640.94550388,3707.52926708,3804.01479785,3870.59856106,3956.55593507,4029.28682081,4071.87477095,4181.82795803,4234.94406493,4320.90143894,4344.89725201,4440.60130905,4513.33219479,4599.28956881,4689.62797704,4762.35886279,4842.16911426,4914.9,4987.63088574,5058.19037282,5120.55724412,5193.28812986,5279.24550388,5345.82926708,5442.31479785,5508.89856106,5594.85593507,5667.58682081,5710.17477095,5820.12795803,5873.24406493,5959.20143894,5983.19725201,6078.90130905,6151.63219479,6237.58956881,6327.92797704,6400.65886279,6480.46911426,6553.2,6625.93088574,6696.49037282,6758.85724412,6831.58812986,6917.54550388,6984.12926708,7080.61479785,7147.19856106,7233.15593507,7305.88682081,7348.47477095,7458.42795803,7511.54406493,7597.50143894,7621.49725201,7717.20130905,7789.93219479,7875.88956881,7966.22797704,8038.95886279,8118.76911426,8191.5,8264.23088574,8334.79037282,8397.15724412,8469.88812986,8555.84550388,8622.42926708,8718.91479785,8785.49856106,8871.45593507,8944.18682081,8986.77477095,9096.72795803,9149.84406493,9235.80143894,9259.79725201,9355.50130905,9428.23219479,9514.18956881,9604.52797704,9677.25886279,9757.06911426,9829.8,9902.53088574,9973.09037282,10035.4572441,10108.1881299,10194.1455039,10260.7292671,10357.2147979,10423.7985611,10509.7559351,10582.4868208,10625.074771,10735.027958,10788.1440649,10874.1014389,10898.097252,10993.801309,11066.5321948,11152.4895688,11242.827977,11315.5588628,11395.3691143,11468.1,11540.8308857,11611.3903728,11673.7572441,11746.4881299,11832.4455039,11899.0292671,11995.5147979,12062.0985611,12148.0559351,12220.7868208,12263.374771,12373.327958,12426.4440649,12512.4014389,12536.397252,12632.101309,12704.8321948,12790.7895688,12881.127977,12953.8588628,13033.6691143,13106.4,13179.1308857,13249.6903728,13312.0572441,13384.7881299,13470.7455039,13537.3292671,13633.8147979,13700.3985611,13786.3559351,13859.0868208,13901.674771,14011.627958,14064.7440649,14150.7014389,14174.697252,14270.401309,14343.1321948,14429.0895688,14519.427977,14592.1588628,14671.9691143,14744.7,14817.4308857,14887.9903728,14950.3572441,15023.0881299,15109.0455039,15175.6292671,15272.1147979,15338.6985611,15424.6559351,15497.3868208,15539.974771,15649.927958,15703.0440649,15789.0014389,15812.997252,15908.701309,15981.4321948,16067.3895688,16157.727977,16230.4588628,16310.2691143,16383.0,16455.7308857 };
const float Quantizer::freqs15[] = { 8.17579891564,8.43129263176,8.68678634787,8.91905336252,9.1977737801,9.53843206825,9.81095869877,10.2197486446,10.511741463,10.9010652209,11.241723509,11.4461184819,11.9911717429,12.2636983735,12.7179094243,12.8476840103,13.3785800438,13.7966606701,14.3076481024,14.8650889375,15.3296229668,15.8560948667,16.3515978313,16.8625852635,17.3735726957,17.838106725,18.3955475602,19.0768641365,19.6219173975,20.4394972891,21.0234829259,21.8021304417,22.483447018,22.8922369638,23.9823434859,24.5273967469,25.4358188487,25.6953680206,26.7571600876,27.5933213403,28.6152962048,29.7301778751,30.6592459337,31.7121897334,32.7031956626,33.725170527,34.7471453915,35.6762134501,36.7910951204,38.153728273,39.2438347951,40.8789945782,42.0469658519,43.6042608834,44.966894036,45.7844739276,47.9646869718,49.0547934939,50.8716376973,51.3907360412,53.5143201751,55.1866426806,57.2305924095,59.4603557501,61.3184918673,63.4243794668,65.4063913251,67.4503410541,69.494290783,71.3524269002,73.5821902408,76.307456546,78.4876695902,81.7579891564,84.0939317038,87.2085217669,89.9337880721,91.5689478552,95.9293739436,98.1095869877,101.743275395,102.781472082,107.02864035,110.373285361,114.461184819,118.9207115,122.636983735,126.848758934,130.81278265,134.900682108,138.988581566,142.7048538,147.164380482,152.614913092,156.97533918,163.515978313,168.187863408,174.417043534,179.867576144,183.13789571,191.858747887,196.219173975,203.486550789,205.562944165,214.0572807,220.746570722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
const int *Quantizer::hints[] = { hints0,hints1,hints2,hints3,hints4,hints5,hints6,hints7,hints8,hints9,hints10,hints11,hints12,hints13,hints14,hints15,hints16 };


// END AUTOGENERATED SCALE CLASS DATA
